giovi321/ios-backup-machine/app/webui.py

#!/usr/bin/env python3
"""
webui.py - Web UI for iOS Backup Machine settings.

Provides a web interface to configure:
- General settings (date, backup dir, owner info)
- WiFi
- NTP
- Notifications (webhook, MQTT)
- WireGuard client
- Web UI interface binding
All configuration is saved directly to config.yaml.
"""
import os, sys, time, subprocess, json, secrets, yaml, copy, hashlib, glob, plistlib, logging, shlex, shutil, threading
from functools import wraps
from logging.handlers import RotatingFileHandler

from flask import (
    Flask, render_template, request, redirect, url_for,
    flash, jsonify, send_from_directory, session
)

import netutil
import wg_crypto
import wg_manager
import wifi_manager
import host_key
import sync_crypto
import sync_manager
import notify_crypto
import config_schema
import power
import logutil

VERSION = "4.11.1"

CONFIG_PATH = os.getenv("IOSBACKUP_CONFIG", "/root/iosbackupmachine/config.yaml")
STATIC_DIR = os.path.join(os.path.dirname(os.path.abspath(__file__)), "webui_static")
TEMPLATE_DIR = os.path.join(os.path.dirname(os.path.abspath(__file__)), "webui_templates")

app = Flask(
    __name__,
    template_folder=TEMPLATE_DIR,
    static_folder=STATIC_DIR,
    static_url_path="/static"
)

# The only upload is /api/import-config, and an exported config.yaml is a few KB
# (the shipped example is 5 KB). Without a cap, picking the wrong file in the
# browser — a photo, a backup archive — has api_import_config read the whole body
# into RAM and hand it to PyYAML on a 512 MB board. 256 KB is ~50x a real config
# and stays under Flask's own 500 KB form-field limit, so this is always the
# limit that bites first and the number in the 413 message is always the true one.
MAX_UPLOAD_BYTES = 256 * 1024
app.config["MAX_CONTENT_LENGTH"] = MAX_UPLOAD_BYTES

# A wholesale wrong file can mistype every key in DEFAULTS; show the first few
# and leave the rest to webui.log rather than burying the page in banners.
IMPORT_WARNING_LIMIT = 10

@app.context_processor
def inject_version():
    return {"app_version": VERSION,
            "config_warnings": config_schema.get_load_warnings(),
            "pending_confirm": _pending_confirm()}

# Persistent logs on the rootfs; runtime status/flags on the volatile zram
# /var/log. See logutil.py for the rationale.
LOG_DIR = logutil.LOG_DIR
RUNTIME_DIR = logutil.RUNTIME_DIR

# --- Logging setup ---
os.makedirs(LOG_DIR, exist_ok=True)
os.makedirs(RUNTIME_DIR, exist_ok=True)
_log_handler = RotatingFileHandler(
    os.path.join(LOG_DIR, "webui.log"), maxBytes=2*1024*1024, backupCount=3
)
_log_handler.setFormatter(logging.Formatter("%(asctime)s [%(levelname)s] %(message)s", datefmt="%Y-%m-%d %H:%M:%S"))
_log_handler.setLevel(logging.INFO)
app.logger.addHandler(_log_handler)
app.logger.setLevel(logging.INFO)
logging.getLogger("werkzeug").setLevel(logging.WARNING)

# ---------------------------------------------------------------------------
# Config helpers
# ---------------------------------------------------------------------------

def load_config():
    # config_schema is the single source of defaults + the migration step.
    return config_schema.load_config(CONFIG_PATH)

def _apply_defaults(cfg):
    # Kept for backward compatibility; defaults now live in config_schema.
    return config_schema.apply_defaults(cfg)

# ---------------------------------------------------------------------------
# Authentication helpers
# ---------------------------------------------------------------------------

def _hash_password(password):
    """Hash a password using SHA-256 + salt (no bcrypt dependency needed)."""
    salt = secrets.token_hex(16)
    h = hashlib.sha256((salt + password).encode("utf-8")).hexdigest()
    return f"{salt}${h}"

def _verify_password(password, stored_hash):
    """Verify password against stored salt$hash."""
    if not stored_hash or "$" not in stored_hash:
        return False
    salt, h = stored_hash.split("$", 1)
    return hashlib.sha256((salt + password).encode("utf-8")).hexdigest() == h

def _auth_enabled():
    cfg = load_config()
    return bool(cfg.get("auth", {}).get("password_hash", ""))

def login_required(f):
    @wraps(f)
    def decorated(*args, **kwargs):
        if _setup_needed():
            return redirect(url_for("setup"))
        if _auth_enabled() and not session.get("authenticated"):
            return redirect(url_for("login", next=request.path))
        return f(*args, **kwargs)
    return decorated

def save_config(cfg):
    # Atomic write (tmp + fsync + rename) — a power loss mid-save can no longer
    # truncate config.yaml.
    config_schema.atomic_save(cfg, CONFIG_PATH)


def _try_save_config(cfg):
    """Persist config from a request handler; on failure flash the reason and
    return False so the caller can re-render/redirect instead of 500ing."""
    try:
        save_config(cfg)
        return True
    except Exception as e:
        app.logger.exception("Could not save configuration")
        flash(f"Could not save configuration: {e}", "error")
        return False


# ---------------------------------------------------------------------------
# WiFi multi-network helpers
# ---------------------------------------------------------------------------
def _wifi_networks(cfg):
    """Return the configured WiFi networks as a list of {nickname, ssid, password}.
    Falls back to the single legacy ssid/password if no networks list exists yet."""
    wifi = cfg.get("wifi", {}) or {}
    nets = wifi.get("networks")
    if nets:
        return nets
    ssid = (wifi.get("ssid") or "").strip()
    if ssid:
        return [{"nickname": "", "ssid": ssid, "password": wifi.get("password", "")}]
    return []


def _wifi_nickname_for(cfg, ssid):
    """Nickname configured for ``ssid`` (the live connected network), or ''."""
    if not ssid:
        return ""
    for net in _wifi_networks(cfg):
        if (net.get("ssid") or "") == ssid:
            return (net.get("nickname") or "").strip()
    return ""

# ---------------------------------------------------------------------------
# First-start / secret-key helpers
# ---------------------------------------------------------------------------

_PLACEHOLDER_KEYS = {"", "change-me", "change-me-to-a-random-string"}

def _ensure_secret_key():
    """
    If the secret_key in config.yaml is a placeholder (or empty),
    generate a cryptographically random one and persist it.
    Returns the (possibly new) secret key.
    """
    cfg = load_config()
    webui = cfg.get("webui", {})
    current = webui.get("secret_key", "")
    if current in _PLACEHOLDER_KEYS:
        new_key = secrets.token_hex(32)
        webui["secret_key"] = new_key
        cfg["webui"] = webui
        try:
            save_config(cfg)
            app.logger.info("Auto-generated new secret key.")
        except Exception as e:
            # Keep serving with the in-memory key; sessions just won't survive
            # a restart until the config becomes writable again.
            app.logger.error("Could not persist new secret key: %s", e)
        return new_key
    return current

def _setup_needed():
    """Return True if the guided first-start wizard should be shown."""
    cfg = load_config()
    # A missing/corrupt config means the saved setup state (and password hash)
    # is gone; the wizard is the recovery path, so re-engage it rather than
    # leaving an open UI that pretends setup was done.
    if config_schema.was_load_degraded():
        return True
    return not cfg.get("setup_completed", False)

# ---------------------------------------------------------------------------
# Global error handler
# ---------------------------------------------------------------------------

@app.errorhandler(Exception)
def _unhandled_error(e):
    """Log the full traceback and render a friendly page instead of the Werkzeug
    500. Debug stays off, so nothing internal leaks to the browser."""
    from werkzeug.exceptions import HTTPException
    if isinstance(e, HTTPException):
        return e
    app.logger.exception("Unhandled error on %s %s", request.method, request.path)
    try:
        return render_template("error.html"), 500
    except Exception:
        return "Something went wrong — see the Logs page.", 500

@app.errorhandler(413)
def _upload_too_large(e):
    """_unhandled_error hands HTTPExceptions straight back, so an oversized POST
    lands on Werkzeug's bare "Request Entity Too Large" page with no sidebar and
    no way back. Refuse it the way every other refused action is refused: a flash
    and a redirect to the page the user was on."""
    app.logger.warning("Rejected oversized %s to %s (%s bytes)",
                       request.method, request.path, request.content_length)
    flash(f"Upload rejected: the request was larger than the "
          f"{MAX_UPLOAD_BYTES // 1024} KB limit. An exported config.yaml is only "
          "a few KB, so check you picked the right file.", "error")
    return redirect(request.referrer or url_for("settings_general"))

# ---------------------------------------------------------------------------
# Routes
# ---------------------------------------------------------------------------

@app.route("/setup", methods=["GET", "POST"])
def setup():
    """Guided first-start wizard."""
    cfg = load_config()
    if not _setup_needed():
        return redirect(url_for("index"))

    # Detect connected iPhone for encryption & device filter steps
    connected_udid = wg_crypto.get_iphone_udid()
    connected_name = ""
    if connected_udid:
        try:
            r = subprocess.run(["ideviceinfo", "-k", "DeviceName"],
                               capture_output=True, text=True, timeout=5)
            connected_name = r.stdout.strip() if r.returncode == 0 else ""
        except Exception:
            pass

    current_time = time.strftime("%Y-%m-%dT%H:%M")

    if request.method == "POST":
        # Pairing is handled via /api/pair AJAX call before form submit.
        # Re-detect iPhone in case it was paired during this session.
        connected_udid = wg_crypto.get_iphone_udid()

        # --- Step 1: Owner info ---
        owner = []
        for i in range(4):
            owner.append(request.form.get(f"owner_line_{i}", ""))
        cfg["owner_lines"] = owner

        # --- Step 2: WiFi ---
        # The setup wizard collects a single network; it seeds wifi.networks so
        # the rest of the app (and the WiFi settings page) use the same model.
        wifi = cfg.get("wifi", {})
        wifi["enabled"] = request.form.get("wifi_enabled") == "on"
        wifi_ssid = request.form.get("wifi_ssid", "").strip()
        wifi_password = request.form.get("wifi_password", "")
        wifi["ssid"] = wifi_ssid
        wifi["password"] = wifi_password
        wifi["networks"] = ([{"nickname": "", "ssid": wifi_ssid, "password": wifi_password}]
                            if wifi_ssid else [])
        cfg["wifi"] = wifi
        if wifi["enabled"] and wifi_ssid:
            _apply_wifi_networks(wifi["networks"])

        # --- Step 3: Date/Time & NTP ---
        new_dt = request.form.get("setup_datetime", "").strip()
        if new_dt and new_dt != current_time:
            try:
                subprocess.run(["date", "-s", new_dt.replace("T", " ")],
                               capture_output=True, text=True, timeout=5)
                # Update RTC
                try:
                    import socket
                    s = socket.create_connection(("127.0.0.1", 8423), timeout=5)
                    s.sendall(b"rtc_pi2rtc\n")
                    time.sleep(0.5)
                    s.close()
                except Exception:
                    pass
                flash("Date/time updated.", "success")
            except Exception as e:
                flash(f"Failed to set date: {e}", "warning")

        ntp = cfg.get("ntp", {})
        ntp["enabled"] = request.form.get("ntp_enabled") == "on"
        servers = request.form.get("ntp_servers", "").strip().splitlines()
        ntp["servers"] = [s.strip() for s in servers if s.strip()]
        cfg["ntp"] = ntp

        # --- Step 4: Backup directory ---
        bd = request.form.get("backup_dir", "").strip()
        if bd:
            cfg["backup_dir"] = bd

        # --- Step 5: Backup encryption ---
        enc_pw = request.form.get("encryption_password", "").strip()
        enc_pw_confirm = request.form.get("encryption_password_confirm", "").strip()
        if enc_pw:
            if enc_pw != enc_pw_confirm:
                flash("Encryption passwords do not match.", "error")
                return render_template("setup.html", cfg=cfg,
                                       connected_udid=connected_udid,
                                       connected_name=connected_name,
                                       current_time=current_time)
            if connected_udid:
                try:
                    r = subprocess.run(
                        ["idevicebackup2", "encryption", "on", enc_pw,
                         cfg.get("backup_dir", "/media/iosbackup/")],
                        capture_output=True, text=True, timeout=60
                    )
                    out = r.stdout + r.stderr
                    if r.returncode == 0 or "enabled" in out.lower():
                        enc = cfg.get("backup_encryption", {})
                        enc["encryption_confirmed"] = True
                        cfg["backup_encryption"] = enc
                        flash("Backup encryption enabled on your iPhone.", "success")
                    else:
                        flash(f"Could not enable encryption: {out[:150]}. "
                              "Go to Encryption settings later to retry.", "warning")
                except subprocess.TimeoutExpired:
                    flash("Encryption command timed out. Make sure iPhone is unlocked. "
                          "You can retry from the Encryption page.", "warning")
                except Exception as e:
                    flash(f"Encryption error: {e}. You can retry from the Encryption page.", "warning")
            else:
                flash("No iPhone connected - encryption password was NOT stored. "
                      "Connect your iPhone and visit the Encryption page to enable it.", "warning")

        # --- Step 6: Device filter ---
        df = cfg.get("device_filter", {})
        df["enabled"] = request.form.get("filter_enabled") == "on"
        if connected_udid and request.form.get("add_connected_device") == "on":
            allowed = df.get("allowed_devices", [])
            existing_udids = [d.get("udid", "") for d in allowed]
            if connected_udid not in existing_udids:
                name = connected_name or "iPhone"
                allowed.append({"udid": connected_udid, "name": name})
                df["allowed_devices"] = allowed
                flash(f"Added device: {name} ({connected_udid})", "success")
        cfg["device_filter"] = df

        # --- Step 7: Notifications ---
        notif = cfg.get("notifications", {})
        # Webhook
        wh = notif.get("webhook", {})
        wh["enabled"] = request.form.get("webhook_enabled") == "on"
        wh["url"] = request.form.get("webhook_url", "")
        wh_events = request.form.getlist("webhook_events")
        if wh_events:
            wh["events"] = wh_events
        notif["webhook"] = wh
        # MQTT
        mq = notif.get("mqtt", {})
        mq["enabled"] = request.form.get("mqtt_enabled") == "on"
        mq["broker"] = request.form.get("mqtt_broker", "")
        try:
            mq["port"] = int(request.form.get("mqtt_port", "1883"))
        except ValueError:
            mq["port"] = 1883
        mq["username"] = request.form.get("mqtt_username", "")
        mq["password"] = request.form.get("mqtt_password", "")
        mq["topic_prefix"] = request.form.get("mqtt_topic_prefix", "iosbackupmachine")
        mq_events = request.form.getlist("mqtt_events")
        if mq_events:
            mq["events"] = mq_events
        notif["mqtt"] = mq
        cfg["notifications"] = notif

        # --- Step 8: Orientation ---
        orient = request.form.get("orientation", "")
        if orient:
            cfg["orientation"] = orient

        # --- Step 9: Web UI password ---
        pw = request.form.get("password", "").strip()
        if pw:
            confirm = request.form.get("confirm_password", "")
            if pw != confirm:
                flash("Passwords do not match.", "error")
                return render_template("setup.html", cfg=cfg,
                                       connected_udid=connected_udid,
                                       connected_name=connected_name,
                                       current_time=current_time)
            if len(pw) < 4:
                flash("Password must be at least 4 characters.", "error")
                return render_template("setup.html", cfg=cfg,
                                       connected_udid=connected_udid,
                                       connected_name=connected_name,
                                       current_time=current_time)
            auth = cfg.get("auth", {})
            auth["password_hash"] = _hash_password(pw)
            cfg["auth"] = auth
            session["authenticated"] = True

        cfg["setup_completed"] = True
        if not _try_save_config(cfg):
            return redirect(url_for("setup"))

        # If iPhone is connected, restart the backup service so it picks up
        # the newly-completed setup without requiring a re-plug.
        if connected_udid:
            try:
                subprocess.run(["systemctl", "restart", "iosbackupmachine.service"],
                               capture_output=True, timeout=5)
            except Exception:
                pass

        flash("Setup complete! Your iOS Backup Machine is ready.", "success")
        return redirect(url_for("index"))

    return render_template("setup.html", cfg=cfg,
                           connected_udid=connected_udid,
                           connected_name=connected_name,
                           current_time=current_time)

@app.route("/login", methods=["GET", "POST"])
def login():
    if _setup_needed():
        return redirect(url_for("setup"))
    if not _auth_enabled():
        return redirect(url_for("index"))
    if request.method == "POST":
        pw = request.form.get("password", "")
        cfg = load_config()
        stored = cfg.get("auth", {}).get("password_hash", "")
        if _verify_password(pw, stored):
            session["authenticated"] = True
            next_url = request.args.get("next", url_for("index"))
            return redirect(next_url)
        flash("Incorrect password.", "error")
    return render_template("login.html")

@app.route("/logout")
def logout():
    session.pop("authenticated", None)
    flash("Logged out.", "success")
    return redirect(url_for("login"))

def _read_backup_status():
    """Read backup status from the status file written by iosbackupmachine.py."""
    status_file = os.path.join(RUNTIME_DIR, "backup_status.json")
    try:
        if os.path.exists(status_file):
            with open(status_file, "r") as f:
                return json.load(f)
    except Exception:
        pass
    return None


def _get_storage_info():
    """Get storage info for backup drive and root."""
    info = {}
    for name, path in [("root", "/"), ("backup", load_config().get("backup_dir", "/media/iosbackup/"))]:
        try:
            st = os.statvfs(path)
            total = st.f_blocks * st.f_frsize
            free = st.f_bavail * st.f_frsize
            used = total - free
            info[name] = {
                "total": _human_size(total),
                "used": _human_size(used),
                "free": _human_size(free),
                "percent": round(used / total * 100, 1) if total > 0 else 0,
            }
        except Exception:
            info[name] = None
    return info

@app.route("/")
@login_required
def index():
    cfg = load_config()
    ip, iface_type = netutil.get_active_ip()
    wg_status = wg_manager.get_wireguard_status(cfg.get("wireguard", {}).get("interface_name", "wg0"))
    backup_status = _read_backup_status()
    storage = _get_storage_info()
    wifi_ssid = netutil.get_wifi_ssid()
    connectivity.ensure_started()
    return render_template("index.html", cfg=cfg, ip=ip, iface_type=iface_type,
                           wg_status=wg_status, backup_status=backup_status, storage=storage,
                           wifi_ssid=wifi_ssid, wifi_nickname=_wifi_nickname_for(cfg, wifi_ssid),
                           connectivity=connectivity.snapshot())

@app.route("/favicon.ico")
def favicon():
    return send_from_directory(STATIC_DIR, "favicon.ico", mimetype="image/x-icon")

# --- General Settings ---
@app.route("/settings/general", methods=["GET", "POST"])
@login_required
def settings_general():
    cfg = load_config()
    if request.method == "POST":
        cfg["backup_dir"] = request.form.get("backup_dir", cfg["backup_dir"])
        cfg["marker_file"] = request.form.get("marker_file", cfg["marker_file"])
        cfg["disk_device"] = request.form.get("disk_device", cfg["disk_device"])
        cfg["orientation"] = request.form.get("orientation", cfg["orientation"])
        cfg["font_path"] = request.form.get("font_path", cfg["font_path"])
        # Owner lines
        owner = []
        for i in range(4):
            owner.append(request.form.get(f"owner_line_{i}", ""))
        cfg["owner_lines"] = owner
        if _try_save_config(cfg):
            flash("General settings saved.", "success")
        return redirect(url_for("settings_general"))
    return render_template("settings_general.html", cfg=cfg)

# --- Date/Time ---
@app.route("/settings/datetime", methods=["GET", "POST"])
@login_required
def settings_datetime():
    cfg = load_config()
    current_time = time.strftime("%Y-%m-%dT%H:%M")
    if request.method == "POST":
        action = request.form.get("action", "")
        if action == "set_date":
            new_dt = request.form.get("datetime", "")
            if new_dt:
                try:
                    subprocess.run(["date", "-s", new_dt.replace("T", " ")],
                                   capture_output=True, text=True, timeout=5)
                    # Update RTC
                    try:
                        import socket
                        s = socket.create_connection(("127.0.0.1", 8423), timeout=5)
                        s.sendall(b"rtc_pi2rtc\n")
                        time.sleep(0.5)
                        s.close()
                    except Exception:
                        pass
                    flash("Date/time updated.", "success")
                except Exception as e:
                    flash(f"Failed to set date: {e}", "error")
        elif action == "ntp_sync":
            try:
                r = subprocess.run(
                    [sys.executable, os.path.join(os.path.dirname(__file__), "ntp-sync.py")],
                    capture_output=True, text=True, timeout=30,
                    env={**os.environ, "IOSBACKUP_CONFIG": CONFIG_PATH}
                )
                if r.returncode == 0:
                    flash("NTP sync completed.", "success")
                else:
                    flash(f"NTP sync failed: {r.stderr[:200]}", "error")
            except Exception as e:
                flash(f"NTP sync error: {e}", "error")
        elif action == "save_ntp":
            ntp = cfg.get("ntp", {})
            ntp["enabled"] = request.form.get("ntp_enabled") == "on"
            servers = request.form.get("ntp_servers", "").strip().splitlines()
            ntp["servers"] = [s.strip() for s in servers if s.strip()]
            cfg["ntp"] = ntp
            if _try_save_config(cfg):
                flash("NTP settings saved.", "success")
        elif action == "set_timezone":
            tz = request.form.get("timezone", "").strip()
            if tz:
                try:
                    subprocess.run(["timedatectl", "set-timezone", tz],
                                   capture_output=True, text=True, timeout=5, check=True)
                    flash(f"Timezone set to {tz}.", "success")
                except subprocess.CalledProcessError as e:
                    flash(f"Invalid timezone: {tz}", "error")
                except Exception as e:
                    flash(f"Failed to set timezone: {e}", "error")
        elif action == "sync_browser":
            browser_time = request.form.get("browser_time", "").strip()
            if browser_time:
                try:
                    subprocess.run(["date", "-s", browser_time],
                                   capture_output=True, text=True, timeout=5)
                    try:
                        import socket as _sock
                        s = _sock.create_connection(("127.0.0.1", 8423), timeout=5)
                        s.sendall(b"rtc_pi2rtc\n")
                        time.sleep(0.5)
                        s.close()
                    except Exception:
                        pass
                    flash("Clock synced with your browser.", "success")
                except Exception as e:
                    flash(f"Failed to sync: {e}", "error")
        return redirect(url_for("settings_datetime"))
    # Get current timezone
    current_tz = ""
    try:
        r = subprocess.run(["timedatectl", "show", "--property=Timezone", "--value"],
                           capture_output=True, text=True, timeout=5)
        current_tz = r.stdout.strip()
    except Exception:
        pass
    return render_template("settings_datetime.html", cfg=cfg, current_time=current_time,
                           current_tz=current_tz)

# --- WiFi ---
@app.route("/settings/wifi", methods=["GET", "POST"])
@login_required
def settings_wifi():
    cfg = load_config()
    if request.method == "POST":
        # Parse the dynamic rows. The three fields are parallel lists; a row is
        # kept only if it has an SSID (nickname and password are optional).
        nicknames = request.form.getlist("nickname")
        ssids = request.form.getlist("ssid")
        passwords = request.form.getlist("password")
        networks = []
        for i, ssid in enumerate(ssids):
            ssid = (ssid or "").strip()
            if not ssid:
                continue
            networks.append({
                "nickname": (nicknames[i] if i < len(nicknames) else "").strip(),
                "ssid": ssid,
                "password": passwords[i] if i < len(passwords) else "",
            })
        wifi = cfg.get("wifi", {})
        wifi["enabled"] = request.form.get("wifi_enabled") == "on"
        wifi["networks"] = networks
        # Keep the legacy single-network fields mirrored to the first entry so
        # older readers (and a downgrade) still see a sane value.
        wifi["ssid"] = networks[0]["ssid"] if networks else ""
        wifi["password"] = networks[0]["password"] if networks else ""
        cfg["wifi"] = wifi
        if not _try_save_config(cfg):
            return redirect(url_for("settings_wifi"))
        if wifi["enabled"] and networks:
            ok, msg = _apply_wifi_networks(networks)
            flash(f"WiFi settings saved. {msg}" if ok
                  else f"Saved, but applying WiFi failed: {msg}",
                  "success" if ok else "error")
        else:
            flash("WiFi settings saved.", "success")
        return redirect(url_for("settings_wifi"))
    wifi_ip = netutil.get_wifi_ip()
    wifi_ssid = netutil.get_wifi_ssid()
    return render_template("settings_wifi.html", cfg=cfg, wifi_ip=wifi_ip,
                           wifi_ssid=wifi_ssid,
                           wifi_nickname=_wifi_nickname_for(cfg, wifi_ssid),
                           wifi_networks=_wifi_networks(cfg))

@app.route("/settings/wifi/connect", methods=["POST"])
@login_required
def wifi_connect_inrange():
    """Force a scan and connect to any saved network that's in range."""
    cfg = load_config()
    if not cfg.get("wifi", {}).get("enabled"):
        flash("Enable WiFi and save first.", "error")
        return redirect(url_for("settings_wifi"))
    networks = _wifi_networks(cfg)
    if not networks:
        flash("No WiFi networks configured yet.", "error")
        return redirect(url_for("settings_wifi"))
    ok, info = wifi_manager.scan_and_connect(networks)
    if ok:
        nick = _wifi_nickname_for(cfg, info)   # info is the connected SSID
        label = f"{nick} ({info})" if nick else info
        flash(f"Connected to {label}.", "success")
    else:
        app.logger.error("WiFi scan/connect failed: %s", info)
        flash(info, "error")
    return redirect(url_for("settings_wifi"))

def _apply_wifi_networks(networks):
    """Apply the configured WiFi networks via netplan (see wifi_manager). The
    device has no NetworkManager, so WiFi is managed by writing a netplan drop-in
    and letting wpa_supplicant associate to whichever configured network is in
    range. Returns (ok, message); callers surface the message to the user."""
    ok, msg = wifi_manager.apply_networks(networks)
    if not ok:
        app.logger.error("WiFi apply failed: %s", msg)
    return ok, msg

# --- Notifications ---
@app.route("/settings/notifications", methods=["GET", "POST"])
@login_required
def settings_notifications():
    cfg = load_config()
    if request.method == "POST":
        notif = cfg.get("notifications", {})
        # Webhook
        wh = notif.get("webhook", {})
        wh["enabled"] = request.form.get("webhook_enabled") == "on"
        wh["url"] = request.form.get("webhook_url", "")
        wh_events = request.form.getlist("webhook_events")
        wh["events"] = wh_events
        # Optional auth header. The header NAME is stored in config; the VALUE is
        # encrypted into notify.enc (same credential store as WireGuard/sync).
        wh["auth_enabled"] = request.form.get("webhook_auth_enabled") == "on"
        wh["auth_header"] = (request.form.get("webhook_auth_header", "").strip()
                             or "Authorization")
        auth_value = request.form.get("webhook_auth_value", "")
        if auth_value.strip():
            mode = cfg.get("credential_encryption", {}).get("passphrase_mode", "udid")
            pw = (wg_crypto.get_iphone_serial() if mode == "udid"
                  else request.form.get("master_password", "").strip())
            if not pw:
                flash("Connect iPhone first." if mode == "udid"
                      else "Master password required to save the webhook auth header.", "error")
            elif notify_crypto.encrypt_notify_config(
                    {"header": wh["auth_header"], "value": auth_value.strip()}, passphrase=pw):
                flash("Webhook auth header encrypted and saved.", "success")
            else:
                flash("Failed to encrypt the webhook auth header.", "error")
        notif["webhook"] = wh
        # MQTT
        mq = notif.get("mqtt", {})
        mq["enabled"] = request.form.get("mqtt_enabled") == "on"
        mq["broker"] = request.form.get("mqtt_broker", "")
        try:
            mq["port"] = int(request.form.get("mqtt_port", "1883"))
        except ValueError:
            mq["port"] = 1883
        mq["username"] = request.form.get("mqtt_username", "")
        mq["password"] = request.form.get("mqtt_password", "")
        mq["topic_prefix"] = request.form.get("mqtt_topic_prefix", "iosbackupmachine")
        mq_events = request.form.getlist("mqtt_events")
        mq["events"] = mq_events
        notif["mqtt"] = mq
        cfg["notifications"] = notif
        if not _try_save_config(cfg):
            return redirect(url_for("settings_notifications"))
        # Drop the cached auth header: the URL, the header name or the secret
        # itself may have just changed, and a stale cached value would keep
        # being sent (and rejected) until the next reboot.
        try:
            import notifications as _notif
            _notif.clear_auth_cache()
        except Exception:
            pass
        flash("Notification settings saved.", "success")
        return redirect(url_for("settings_notifications"))
    return render_template("settings_notifications.html", cfg=cfg,
                           has_notify_enc=os.path.exists(notify_crypto.ENC_FILE))

@app.route("/settings/notifications/test", methods=["POST"])
@login_required
def test_notification():
    """Send a test notification via a specific channel or both."""
    from notifications import send_notification, _send_webhook, _send_mqtt, webhook_auth_headers
    channel = request.form.get("channel", "all")
    cfg = load_config()
    ncfg = cfg.get("notifications", {})
    payload = {
        "event": "test",
        "timestamp": __import__("time").strftime("%Y-%m-%dT%H:%M:%S%z"),
        "source": "iosbackupmachine",
        "message": "Test notification from iOS Backup Machine",
    }
    if channel == "webhook":
        wh = ncfg.get("webhook", {})
        if wh.get("url"):
            extra = webhook_auth_headers(wh)
            if extra is None:
                # Auth is configured but could not be obtained. Sending anyway
                # guarantees a rejection and would report it as a network fault;
                # name the real cause instead. (send_notification makes the same
                # check — this path calls _send_webhook directly and must repeat it.)
                flash("Webhook test not sent: the auth header could not be decrypted. "
                      "Connect the iPhone, or run one backup with it connected so the "
                      "header is cached.", "error")
            else:
                status, err = _send_webhook(wh["url"], payload, extra)
                if status and 200 <= status < 300:
                    flash(f"Webhook test sent successfully (HTTP {status}).", "success")
                else:
                    detail = err or (f"status {status}" if status else "no response")
                    flash(f"Webhook test failed ({detail}).", "error")
        else:
            flash("No webhook URL configured.", "error")
    elif channel == "mqtt":
        mq = ncfg.get("mqtt", {})
        if mq.get("broker"):
            topic = f"{mq.get('topic_prefix', 'iosbackupmachine')}/test"
            ok = _send_mqtt(mq["broker"], mq.get("port", 1883),
                            mq.get("username", ""), mq.get("password", ""),
                            topic, payload)
            if ok:
                flash("MQTT test sent successfully.", "success")
            else:
                flash("MQTT test failed. Check broker settings.", "error")
        else:
            flash("No MQTT broker configured.", "error")
    else:
        send_notification("test", {"message": "Test notification from iOS Backup Machine"})
        flash("Test notification sent to all enabled channels.", "success")
    return redirect(url_for("settings_notifications"))

# --- WireGuard ---
@app.route("/settings/wireguard", methods=["GET", "POST"])
@login_required
def settings_wireguard():
    cfg = load_config()
    wg = cfg.get("wireguard", {})
    iface = wg.get("interface_name", "wg0")
    wg_status = wg_manager.get_wireguard_status(iface)
    udid = wg_crypto.get_iphone_udid()
    has_enc_file = os.path.exists(wg_crypto.ENC_FILE)

    if request.method == "POST":
        action = request.form.get("action", "")
        if action == "save_settings":
            wg["enabled"] = request.form.get("wg_enabled") == "on"
            wg["auto_connect"] = request.form.get("auto_connect") == "on"
            wg["auto_connect_on"] = request.form.getlist("auto_connect_on")
            wg["interface_name"] = request.form.get("interface_name", "wg0")
            wg["full_tunnel"] = request.form.get("full_tunnel") == "on"
            cfg["wireguard"] = wg
            cred_enc = cfg.get("credential_encryption", {})
            cred_enc["passphrase_mode"] = request.form.get("passphrase_mode", "udid")
            cfg["credential_encryption"] = cred_enc
            if not _try_save_config(cfg):
                return redirect(url_for("settings_wireguard"))
            # Apply (or clear) the full-tunnel routing right away if the VPN is
            # already up; otherwise it takes effect on the next connect.
            if wg_manager.is_interface_up(iface):
                if wg["full_tunnel"]:
                    wg_manager.enforce_full_tunnel(iface)
                else:
                    wg_manager.clear_full_tunnel(iface)
            flash("WireGuard settings saved.", "success")
        elif action == "upload_config":
            wg_conf = request.form.get("wg_config", "")
            mode = cfg.get("credential_encryption", {}).get("passphrase_mode", "udid")
            pw = wg_crypto.get_iphone_serial() if mode == "udid" else request.form.get("master_password", "").strip()
            if not wg_conf.strip():
                flash("Empty WireGuard config.", "error")
            elif not pw:
                flash("Connect iPhone first." if mode == "udid" else "Password required.", "error")
            elif wg_crypto.encrypt_wg_config({"wg_conf": wg_conf}, passphrase=pw):
                flash("WireGuard config encrypted and saved.", "success")
            else:
                flash("Failed to encrypt WireGuard config.", "error")
        elif action == "start":
            mode = cfg.get("credential_encryption", {}).get("passphrase_mode", "udid")
            pw = wg_crypto.get_iphone_serial() if mode == "udid" else request.form.get("master_password", "").strip()
            ok, err = wg_manager.start_wireguard(iface, passphrase=pw)
            if ok:
                flash(f"WireGuard interface {iface} started.", "success")
            else:
                flash(f"Failed to start WireGuard: {err}", "error")
        elif action == "stop":
            if wg_manager.stop_wireguard(iface):
                flash(f"WireGuard interface {iface} stopped.", "success")
            else:
                flash("Failed to stop WireGuard.", "error")
        return redirect(url_for("settings_wireguard"))
    mode = cfg.get("credential_encryption", {}).get("passphrase_mode", "udid")
    return render_template("settings_wireguard.html",
                           cfg=cfg, wg_status=wg_status, udid=udid,
                           has_enc_file=has_enc_file, passphrase_mode=mode)

# --- Remote Sync ---
@app.route("/settings/sync", methods=["GET", "POST"])
@login_required
def settings_sync():
    cfg = load_config()
    sync = cfg.get("sync", {})
    udid = wg_crypto.get_iphone_udid()
    has_enc_file = os.path.exists(sync_crypto.ENC_FILE)

    if request.method == "POST":
        action = request.form.get("action", "")
        if action == "save_settings":
            sync["enabled"] = request.form.get("sync_enabled") == "on"
            sync["auto_sync"] = request.form.get("auto_sync") == "on"
            sync["allowed_network"] = request.form.get("allowed_network", "any")
            sync["allowed_ssid"] = request.form.get("allowed_ssid", "").strip()
            # Entered in minutes, stored in seconds. Blank or 0 means no cap, which
            # is the default: the stall watchdogs already kill a sync that has
            # stopped moving, and a first sync of a large backup set legitimately
            # runs for hours. Anything unparseable is treated as no cap rather than
            # silently reinstating one.
            try:
                _cap_min = int(float(request.form.get("max_minutes", "0") or 0))
            except (TypeError, ValueError):
                _cap_min = 0
            sync["max_seconds"] = max(0, _cap_min) * 60
            cfg["sync"] = sync
            if _try_save_config(cfg):
                flash("Sync settings saved.", "success")
        elif action == "upload_credentials":
            mode = cfg.get("credential_encryption", {}).get("passphrase_mode", "udid")
            pw = wg_crypto.get_iphone_serial() if mode == "udid" else request.form.get("master_password", "").strip()
            host = request.form.get("host", "").strip()
            port = request.form.get("port", "22").strip()
            username = request.form.get("username", "").strip()
            auth_method = request.form.get("auth_method", "key")
            ssh_key = request.form.get("ssh_key", "").replace("\r\n", "\n").replace("\r", "\n")
            password = request.form.get("password", "")
            remote_path = request.form.get("remote_path", "").strip()
            verify_host_key = request.form.get("verify_host_key") == "on"
            fingerprint_input = request.form.get("host_key_fingerprint", "").strip()
            if not pw:
                flash("Connect iPhone first." if mode == "udid" else "Password required.", "error")
            elif not host or not username or not remote_path:
                flash("Host, username, and remote path are required.", "error")
            else:
                try:
                    port_int = int(port)
                except ValueError:
                    port_int = 22
                existing_key = ""
                existing_pw = ""
                existing_fp = ""
                if not ssh_key.strip() or not password or not fingerprint_input:
                    try:
                        prev = sync_crypto.decrypt_sync_config(passphrase=pw)
                        if prev:
                            existing_key = prev.get("ssh_key", "")
                            existing_pw = prev.get("password", "")
                            existing_fp = prev.get("host_key_fingerprint", "")
                    except Exception:
                        pass
                final_key = ssh_key if ssh_key.strip() else existing_key
                final_pw = password if password else existing_pw
                # Unticking the checkbox is the only way to turn verification
                # off, so a blank field can safely mean "keep what's stored".
                final_fp = ""
                if verify_host_key:
                    try:
                        final_fp = host_key.normalize_fingerprint(fingerprint_input or existing_fp)
                    except ValueError as e:
                        flash(str(e), "error")
                        return redirect(url_for("settings_sync"))
                    if not final_fp:
                        flash("Enter the server's SHA256 host key fingerprint, or untick host key verification.", "error")
                        return redirect(url_for("settings_sync"))
                if auth_method == "key" and not final_key.strip():
                    flash("SSH private key is required for key authentication.", "error")
                    return redirect(url_for("settings_sync"))
                elif auth_method == "password" and not final_pw:
                    flash("Password is required for password authentication.", "error")
                    return redirect(url_for("settings_sync"))
                cred = {
                    "host": host, "port": port_int, "username": username,
                    "auth_method": auth_method,
                    "ssh_key": final_key if auth_method == "key" else "",
                    "password": final_pw if auth_method == "password" else "",
                    "remote_path": remote_path,
                    "host_key_fingerprint": final_fp,
                }
                if sync_crypto.encrypt_sync_config(cred, passphrase=pw):
                    flash("Sync credentials encrypted and saved.", "success")
                else:
                    flash("Failed to encrypt sync credentials.", "error")
        elif action == "test_connection":
            mode = cfg.get("credential_encryption", {}).get("passphrase_mode", "udid")
            pw = wg_crypto.get_iphone_serial() if mode == "udid" else request.form.get("master_password", "").strip()
            result = sync_manager.test_connection(passphrase=pw)
            flash(result["message"], "success" if result["success"] else "error")
        elif action == "run_sync":
            _cur = _read_backup_status() or {}
            if _cur.get("state") == "syncing":
                flash("Sync is already in progress.", "error")
            # Mutual exclusion, same check the dashboard button makes. backup-sync.py
            # still refuses to run during a backup, but its guard no longer writes the
            # status file (that write clobbered the backup's own state), so the
            # launcher is now the only place the user can be told.
            elif _backup_in_progress():
                flash("A backup is in progress. Wait for it to finish (or use auto-sync).", "error")
            else:
                # Nuke leftovers from a cancelled/crashed sync before relaunching
                try:
                    subprocess.run(["pkill", "-9", "-f", "backup-sync.py"],
                                   capture_output=True, timeout=5)
                    subprocess.run(["pkill", "-9", "-f", "/usr/bin/rsync"],
                                   capture_output=True, timeout=5)
                    time.sleep(0.3)
                except Exception:
                    pass
                sync_script = os.path.join(os.path.dirname(os.path.abspath(__file__)), "backup-sync.py")
                try:
                    _launch_sync_detached(sync_script)
                    flash("Sync started. Check the dashboard for progress.", "success")
                except Exception as e:
                    flash(f"Failed to start sync: {e}", "error")
        return redirect(url_for("settings_sync"))
    mode = cfg.get("credential_encryption", {}).get("passphrase_mode", "udid")
    saved_cred = None
    if has_enc_file:
        try:
            pw = wg_crypto.get_iphone_serial() if mode == "udid" else None
            if pw:
                dec = sync_crypto.decrypt_sync_config(passphrase=pw)
                if dec:
                    saved_cred = {
                        "host": dec.get("host", ""),
                        "port": dec.get("port", 22),
                        "username": dec.get("username", ""),
                        "auth_method": dec.get("auth_method", "key"),
                        "remote_path": dec.get("remote_path", ""),
                        "host_key_fingerprint": dec.get("host_key_fingerprint", ""),
                    }
        except Exception:
            pass
    return render_template("settings_sync.html",
                           cfg=cfg, udid=udid, has_enc_file=has_enc_file,
                           passphrase_mode=mode, saved_cred=saved_cred,
                           backup_status=_read_backup_status())

@app.route("/api/sync/decrypt", methods=["POST"])
@login_required
def api_sync_decrypt():
    """Return full decrypted sync credentials as JSON (excluding sensitive fields in the key)."""
    cfg = load_config()
    mode = cfg.get("credential_encryption", {}).get("passphrase_mode", "udid")
    pw = wg_crypto.get_iphone_serial() if mode == "udid" else None
    if not pw:
        return jsonify({"error": "iPhone not connected"}), 400
    try:
        dec = sync_crypto.decrypt_sync_config(passphrase=pw)
    except Exception as e:
        # A corrupt sync.enc must surface as a clean JSON error, not a 500.
        app.logger.exception("Failed to decrypt sync credentials")
        return jsonify({"error": f"Cannot decrypt credentials: {e}"}), 400
    if not dec:
        return jsonify({"error": "Cannot decrypt credentials"}), 400
    return jsonify({
        "host": dec.get("host", ""),
        "port": dec.get("port", 22),
        "username": dec.get("username", ""),
        "auth_method": dec.get("auth_method", "key"),
        "remote_path": dec.get("remote_path", ""),
        "host_key_fingerprint": dec.get("host_key_fingerprint", ""),
        "has_key": bool(dec.get("ssh_key", "").strip()),
        "has_password": bool(dec.get("password", "")),
    })

@app.route("/api/sync/host-key-scan", methods=["POST"])
@login_required
def api_sync_host_key_scan():
    """Report the SSH host keys a server currently offers, for the settings form.

    This is an *unauthenticated* view of the server — it is only a convenience
    for filling the field, so the response also carries the command to confirm
    the value out-of-band. Host and port come from the form rather than the
    stored credentials, so the fingerprint can be fetched before saving.
    """
    data = request.get_json(silent=True) or {}
    host = str(data.get("host", "")).strip()
    try:
        port = int(data.get("port") or 22)
    except (TypeError, ValueError):
        port = 22
    if not host:
        return jsonify({"error": "Enter the host first."}), 400
    try:
        entries = host_key.fetch_fingerprints(host, port)
    except host_key.HostKeyError as e:
        return jsonify({"error": str(e)}), 400
    except Exception as e:
        return jsonify({"error": f"Cannot read the host key: {e}"}), 400
    if not entries:
        return jsonify({"error": f"{host} returned no host key."}), 400
    return jsonify({
        "keys": [{"type": e["type"], "bits": e["bits"], "fingerprint": e["fingerprint"]}
                 for e in entries],
        "confirm_hint": "Confirm on the server with: "
                        "ssh-keygen -lf /etc/ssh/ssh_host_ed25519_key.pub",
    })

# --- Web UI Interface Binding ---
@app.route("/settings/webui", methods=["GET", "POST"])
@login_required
def settings_webui():
    cfg = load_config()
    if request.method == "POST":
        webui = cfg.get("webui", {})
        try:
            webui["port"] = int(request.form.get("port", "8080"))
        except ValueError:
            webui["port"] = 8080
        bind = request.form.getlist("bind_interfaces")
        webui["bind_interfaces"] = bind if bind else ["all"]
        webui["secret_key"] = request.form.get("secret_key", webui.get("secret_key", ""))
        cfg["webui"] = webui
        if _try_save_config(cfg):
            flash("Web UI settings saved. Restart the service to apply binding changes.", "success")
        return redirect(url_for("settings_webui"))
    interfaces = netutil.get_all_interfaces()
    return render_template("settings_webui.html", cfg=cfg, interfaces=interfaces)

# --- Password Management ---
@app.route("/settings/password", methods=["GET", "POST"])
@login_required
def settings_password():
    cfg = load_config()
    has_password = bool(cfg.get("auth", {}).get("password_hash", ""))
    if request.method == "POST":
        action = request.form.get("action", "")
        if action == "set_password":
            current = request.form.get("current_password", "")
            new_pw = request.form.get("new_password", "")
            confirm = request.form.get("confirm_password", "")
            stored = cfg.get("auth", {}).get("password_hash", "")
            # If password is already set, verify current
            if stored and not _verify_password(current, stored):
                flash("Current password is incorrect.", "error")
                return redirect(url_for("settings_password"))
            if not new_pw:
                flash("New password cannot be empty.", "error")
                return redirect(url_for("settings_password"))
            if new_pw != confirm:
                flash("New passwords do not match.", "error")
                return redirect(url_for("settings_password"))
            if len(new_pw) < 4:
                flash("Password must be at least 4 characters.", "error")
                return redirect(url_for("settings_password"))
            auth = cfg.get("auth", {})
            auth["password_hash"] = _hash_password(new_pw)
            cfg["auth"] = auth
            if not _try_save_config(cfg):
                return redirect(url_for("settings_password"))
            session["authenticated"] = True
            flash("Password updated successfully.", "success")
        elif action == "remove_password":
            current = request.form.get("current_password", "")
            stored = cfg.get("auth", {}).get("password_hash", "")
            if stored and not _verify_password(current, stored):
                flash("Current password is incorrect.", "error")
                return redirect(url_for("settings_password"))
            auth = cfg.get("auth", {})
            auth["password_hash"] = ""
            cfg["auth"] = auth
            if _try_save_config(cfg):
                flash("Password removed. Web UI is now open.", "success")
        return redirect(url_for("settings_password"))
    return render_template("settings_password.html", cfg=cfg, has_password=has_password)

# --- Device Filter ---
@app.route("/settings/devices", methods=["GET", "POST"])
@login_required
def settings_devices():
    cfg = load_config()
    df = cfg.get("device_filter", {})
    # Detect currently connected device
    connected_udid = wg_crypto.get_iphone_udid()
    connected_name = ""
    if connected_udid:
        try:
            r = subprocess.run(["ideviceinfo", "-k", "DeviceName"],
                               capture_output=True, text=True, timeout=5)
            connected_name = r.stdout.strip() if r.returncode == 0 else ""
        except Exception:
            pass

    if request.method == "POST":
        action = request.form.get("action", "")
        if action == "save_filter":
            df["enabled"] = request.form.get("filter_enabled") == "on"
            cfg["device_filter"] = df
            if _try_save_config(cfg):
                flash("Device filter settings saved.", "success")
        elif action == "add_connected":
            if not connected_udid:
                flash("No iPhone connected.", "error")
            else:
                allowed = df.get("allowed_devices", [])
                existing_udids = [d.get("udid", "") for d in allowed]
                if connected_udid in existing_udids:
                    flash(f"Device {connected_udid} is already in the list.", "warning")
                else:
                    name = connected_name or request.form.get("device_name", "Unknown")
                    allowed.append({"udid": connected_udid, "name": name})
                    df["allowed_devices"] = allowed
                    cfg["device_filter"] = df
                    if _try_save_config(cfg):
                        flash(f"Added device: {name} ({connected_udid})", "success")
        elif action == "add_manual":
            udid = request.form.get("manual_udid", "").strip()
            name = request.form.get("manual_name", "").strip() or "Manual entry"
            if not udid:
                flash("UDID cannot be empty.", "error")
            else:
                allowed = df.get("allowed_devices", [])
                existing_udids = [d.get("udid", "") for d in allowed]
                if udid in existing_udids:
                    flash(f"Device {udid} is already in the list.", "warning")
                else:
                    allowed.append({"udid": udid, "name": name})
                    df["allowed_devices"] = allowed
                    cfg["device_filter"] = df
                    if _try_save_config(cfg):
                        flash(f"Added device: {name} ({udid})", "success")
        elif action == "remove_device":
            rm_udid = request.form.get("remove_udid", "")
            allowed = df.get("allowed_devices", [])
            df["allowed_devices"] = [d for d in allowed if d.get("udid") != rm_udid]
            cfg["device_filter"] = df
            if _try_save_config(cfg):
                flash(f"Device {rm_udid} removed.", "success")
        return redirect(url_for("settings_devices"))
    return render_template("settings_devices.html", cfg=cfg, df=df,
                           connected_udid=connected_udid, connected_name=connected_name)

# --- Backup Settings ---
@app.route("/settings/backup", methods=["GET", "POST"])
@login_required
def settings_backup():
    cfg = load_config()
    if request.method == "POST":
        bk = cfg.get("backup", {})
        bk["auto_start"] = request.form.get("auto_start") == "on"
        bk["notify_on_rejected"] = request.form.get("notify_on_rejected") == "on"
        cfg["backup"] = bk
        if _try_save_config(cfg):
            flash("Backup settings saved.", "success")
        return redirect(url_for("settings_backup"))
    return render_template("settings_backup.html", cfg=cfg)

# --- Backup Encryption ---
@app.route("/settings/encryption", methods=["GET", "POST"])
@login_required
def settings_encryption():
    cfg = load_config()
    enc = cfg.get("backup_encryption", {})
    connected_udid = wg_crypto.get_iphone_udid()

    # Check current encryption status on device
    enc_status = None
    if connected_udid:
        # Try ideviceinfo with backup domain (where WillEncrypt lives)
        try:
            r = subprocess.run(
                ["ideviceinfo", "--domain", "com.apple.mobile.backup", "-k", "WillEncrypt"],
                capture_output=True, text=True, timeout=10
            )
            val = r.stdout.strip().lower()
            if r.returncode == 0 and val:
                if val in ("true", "1"):
                    enc_status = "enabled"
                elif val in ("false", "0"):
                    enc_status = "disabled"
        except Exception:
            pass
        # Fallback: run idevicebackup2 and parse output
        if enc_status is None:
            try:
                r = subprocess.run(
                    ["idevicebackup2", "backup", "--dry-run", cfg.get("backup_dir", "/media/iosbackup/")],
                    capture_output=True, text=True, timeout=15
                )
                out = (r.stdout + r.stderr).lower()
                if "will be encrypted" in out or "backup encryption is currently enabled" in out:
                    enc_status = "enabled"
                elif "will not be encrypted" in out or "backup encryption is currently disabled" in out:
                    enc_status = "disabled"
            except Exception:
                pass
        # Last fallback: check if encryption was ever confirmed during a backup
        if enc_status is None and cfg.get("backup_encryption", {}).get("encryption_confirmed"):
            enc_status = "enabled"

    if request.method == "POST":
        action = request.form.get("action", "")
        if action == "enable_encryption":
            pw = request.form.get("enable_password", "").strip()
            if not pw:
                flash("Please provide an encryption password.", "error")
            elif not connected_udid:
                flash("No iPhone connected. Connect your iPhone first.", "error")
            else:
                try:
                    r = subprocess.run(
                        ["idevicebackup2", "encryption", "on", pw, cfg.get("backup_dir", "/media/iosbackup/")],
                        capture_output=True, text=True, timeout=60
                    )
                    out = r.stdout + r.stderr
                    if r.returncode == 0 or "enabled" in out.lower():
                        enc["encryption_confirmed"] = True
                        cfg["backup_encryption"] = enc
                        if _try_save_config(cfg):
                            flash("Backup encryption enabled on device. The password was NOT stored - remember it for restores.", "success")
                    else:
                        flash(f"Failed to enable encryption: {out[:200]}", "error")
                except subprocess.TimeoutExpired:
                    flash("Command timed out. Make sure the iPhone is unlocked and trusted.", "error")
                except Exception as e:
                    flash(f"Error enabling encryption: {e}", "error")
        elif action == "change_password":
            old_pw = request.form.get("old_password", "").strip()
            new_pw = request.form.get("new_password", "").strip()
            if not old_pw or not new_pw:
                flash("Both old and new passwords are required.", "error")
            elif not connected_udid:
                flash("No iPhone connected. Connect your iPhone first.", "error")
            else:
                try:
                    r = subprocess.run(
                        ["idevicebackup2", "changepw", old_pw, new_pw, cfg.get("backup_dir", "/media/iosbackup/")],
                        capture_output=True, text=True, timeout=60
                    )
                    out = r.stdout + r.stderr
                    if r.returncode == 0:
                        flash("Encryption password changed on device. The new password was NOT stored - remember it for restores.", "success")
                    else:
                        flash(f"Failed to change password: {out[:200]}", "error")
                except Exception as e:
                    flash(f"Error changing password: {e}", "error")
        return redirect(url_for("settings_encryption"))
    return render_template("settings_encryption.html",
                           cfg=cfg, enc=enc, connected_udid=connected_udid, enc_status=enc_status)

# --- Backup List ---

def _dir_size(path):
    """Return total size in bytes of all files under *path*."""
    total = 0
    try:
        for dirpath, _dirnames, filenames in os.walk(path):
            for f in filenames:
                fp = os.path.join(dirpath, f)
                try:
                    total += os.path.getsize(fp)
                except OSError:
                    pass
    except OSError:
        pass
    return total

def _human_size(nbytes):
    for unit in ("B", "KB", "MB", "GB", "TB"):
        if abs(nbytes) < 1024:
            return f"{nbytes:.1f} {unit}"
        nbytes /= 1024
    return f"{nbytes:.1f} PB"

app.jinja_env.filters["human_size"] = _human_size


def _human_duration(seconds):
    """Compact duration for the dashboard. Same shape as the sync log's, so an
    ETA read on the dashboard and one read in the log look alike."""
    try:
        seconds = int(seconds)
    except (TypeError, ValueError):
        return ""
    if seconds < 60:
        return f"{seconds}s"
    if seconds < 3600:
        return f"{seconds // 60}m"
    return f"{seconds // 3600}h{(seconds % 3600) // 60:02d}m"

app.jinja_env.filters["human_duration"] = _human_duration


class ConnectivityMonitor:
    """Background internet probe, cached for the dashboard and the health endpoint.

    ``netutil.have_connectivity()`` opens a TCP connection and blocks for up to
    its timeout per host, twice when both fail — so probing inline would make the
    status poll as slow as the outage it is meant to report, and would put a
    packet on the resolvers every few seconds for every open browser tab. This
    probes on its own schedule; readers get the cached answer.

    It also records when the current state began. That is the number that matters
    on this device: the iPhone hotspot can drop as a sync starts and the device
    fails over to WiFi, and "offline for 3m" says that happened where a bare
    "offline" does not.
    """

    def __init__(self, interval=20.0):
        self.interval = interval
        self._lock = threading.Lock()
        self._online = None        # None until the first probe lands
        self._checked_at = 0.0
        self._changed_at = 0.0
        self._thread = None

    def ensure_started(self):
        """Start the probe loop once, on first use.

        Deliberately not started at import: importing this module must not open
        sockets, or the test suite would depend on the network.
        """
        with self._lock:
            if self._thread is not None:
                return
            self._thread = threading.Thread(target=self._loop, daemon=True)
        self._thread.start()

    def _loop(self):
        while True:
            self.probe_once()
            time.sleep(self.interval)

    def probe_once(self):
        """Run one probe and fold it into the cached state. Never raises."""
        try:
            online = bool(netutil.have_connectivity(timeout=4))
        except Exception:
            online = False
        now = time.time()
        with self._lock:
            if online != self._online:
                self._changed_at = now
            self._online = online
            self._checked_at = now
        return online

    def snapshot(self):
        """Current state: ``online`` is None while no probe has completed yet,
        which readers must render as "checking" rather than as offline."""
        now = time.time()
        with self._lock:
            return {
                "online": self._online,
                "age_seconds": int(now - self._checked_at) if self._checked_at else None,
                "since_seconds": int(now - self._changed_at) if self._changed_at else None,
                "interval_seconds": int(self.interval),
            }


connectivity = ConnectivityMonitor()


def _health_internet(monitor=None):
    """Internet state for the health endpoint.

    Prefers the monitor's cached answer so the endpoint stays fast, but probes
    directly when the cache is empty or stale: an external monitor polling
    /api/health must not be told the wrong thing just because nobody has opened
    the dashboard recently. ``monitor`` is injectable for tests.
    """
    monitor = connectivity if monitor is None else monitor
    monitor.ensure_started()
    snap = monitor.snapshot()
    age = snap["age_seconds"]
    if snap["online"] is not None and age is not None and age <= monitor.interval * 2:
        return snap["online"]
    return monitor.probe_once()

def _parse_info_plist(plist_path):
    """Parse an iOS backup Info.plist and return a dict of useful fields."""
    info = {}
    try:
        with open(plist_path, "rb") as fp:
            pl = plistlib.load(fp)
        info["device_name"] = pl.get("Device Name", "")
        info["display_name"] = pl.get("Display Name", "")
        info["product_type"] = pl.get("Product Type", "")
        info["product_version"] = pl.get("Product Version", "")
        info["serial_number"] = pl.get("Serial Number", "")
        info["udid"] = pl.get("Target Identifier", "") or pl.get("Unique Identifier", "")
        last_backup = pl.get("Last Backup Date")
        if last_backup:
            info["last_backup"] = last_backup.strftime("%Y-%m-%d %H:%M:%S")
            info["last_backup_ts"] = last_backup.timestamp()
        else:
            info["last_backup"] = ""
            info["last_backup_ts"] = 0
    except Exception:
        pass
    return info

@app.route("/backups")
@login_required
def backups():
    cfg = load_config()
    backup_dir = cfg.get("backup_dir", "/media/iosbackup/")
    backup_list = []
    if os.path.isdir(backup_dir):
        for entry in os.listdir(backup_dir):
            entry_path = os.path.join(backup_dir, entry)
            if not os.path.isdir(entry_path):
                continue
            info_plist = os.path.join(entry_path, "Info.plist")
            if not os.path.exists(info_plist):
                continue
            info = _parse_info_plist(info_plist)
            # Folder modification time as fallback date
            try:
                stat = os.stat(entry_path)
                folder_mtime = time.strftime("%Y-%m-%d %H:%M:%S", time.localtime(stat.st_mtime))
                folder_mtime_ts = stat.st_mtime
            except OSError:
                folder_mtime = ""
                folder_mtime_ts = 0
            # Size calculated asynchronously via /api/backup-sizes
            # Check for Manifest.plist (indicates a completed backup)
            has_manifest = os.path.exists(os.path.join(entry_path, "Manifest.plist"))
            # Check for Status.plist snapshot state
            status_plist = os.path.join(entry_path, "Status.plist")
            snapshot_state = ""
            if os.path.exists(status_plist):
                try:
                    with open(status_plist, "rb") as fp:
                        st = plistlib.load(fp)
                    snapshot_state = st.get("SnapshotState", "")
                except Exception:
                    pass
            # Determine human-readable status
            if has_manifest and snapshot_state != "uploading":
                status = "complete"
                status_label = "Complete"
            elif snapshot_state == "uploading":
                status = "backing_up"
                status_label = "Backing up"
            elif has_manifest:
                status = "complete"
                status_label = "Complete"
            else:
                status = "interrupted"
                status_label = "Interrupted"

            backup_list.append({
                "folder": entry,
                "device_name": info.get("display_name") or info.get("device_name") or entry,
                "product_type": info.get("product_type", ""),
                "ios_version": info.get("product_version", ""),
                "serial": info.get("serial_number", ""),
                "udid": info.get("udid", entry),
                "size": "...",
                "last_backup": info.get("last_backup") or folder_mtime,
                "sort_ts": info.get("last_backup_ts") or folder_mtime_ts,
                "status": status,
                "status_label": status_label,
            })
    # Sort newest first
    backup_list.sort(key=lambda b: b["sort_ts"], reverse=True)
    sync_enabled = cfg.get("sync", {}).get("enabled", False)
    return render_template("backups.html", cfg=cfg, backups=backup_list,
                           backup_dir=backup_dir, sync_enabled=sync_enabled)

# --- Log Viewer ---
# The Logs page is what the user opens once something has already gone wrong,
# so it must not be the next thing to break: view_log used to f.read() the whole
# file and hand it to Jinja to escape and to buffer, which costs several times
# the file in RAM on a board that has 512 MB of it, and a single runaway run can
# leave a very large log. A run log is read from both ends anyway - a backup's
# gates ([CMD], mount, free space, encryption) are at the top and what it died
# of is at the bottom - so the viewer shows both and the download link covers
# the middle.
LOG_VIEW_HEAD_LINES = int(os.getenv("IOSBACKUP_LOG_VIEW_HEAD_LINES", "40"))
LOG_VIEW_TAIL_LINES = int(os.getenv("IOSBACKUP_LOG_VIEW_TAIL_LINES", "500"))
# Hard ceiling on the read whatever the lines look like: a writer wedged
# mid-line leaves a file with no newline in it at all, and a line-counting tail
# on that one reads the whole thing - the exact failure being bounded here.
LOG_VIEW_MAX_BYTES = int(os.getenv("IOSBACKUP_LOG_VIEW_MAX_BYTES",
                                   str(256 * 1024)))

def _decode_lines(raw):
    # Read as bytes and decode with "replace": a window that opens or closes
    # inside a multi-byte character then renders one U+FFFD instead of raising.
    return raw.decode("utf-8", "replace").splitlines(True)

def _read_bounded(path, head_lines, tail_lines, max_bytes):
    """Read the head and the tail of a log without holding the file in memory.

    Returns (text, truncated, size). When truncated, the two halves are
    separated by one notice line naming what is not shown.
    """
    head_bytes = max(1, max_bytes // 8)           # the failure is at the end,
    tail_bytes = max(1, max_bytes - head_bytes)   # so the tail gets the bulk
    with open(path, "rb") as f:
        # fstat on the handle rather than a separate getsize: the size then
        # always describes the inode the bytes came from.
        size = os.fstat(f.fileno()).st_size
        if size <= max_bytes:
            head, tail, windowed = _decode_lines(f.read()), [], False
        else:
            head = _decode_lines(f.read(head_bytes))
            f.seek(size - tail_bytes)
            tail, windowed = _decode_lines(f.read(tail_bytes)), True
    if windowed:
        # Drop the half lines the two windows end and start in, but only while a
        # whole line survives: a log with no newline in it would otherwise come
        # back empty, which is worse than a fragment.
        if len(head) > 1 and not head[-1].endswith("\n"):
            head.pop()
        if len(tail) > 1:
            tail.pop(0)
    elif len(head) <= head_lines + tail_lines:
        return "".join(head), False, size         # short enough to show whole
    else:
        # Under the byte ceiling but past what anyone reads on a phone: split
        # the lines already in hand rather than returning the head alone.
        whole = head
        head, tail = whole[:head_lines], whole[-tail_lines:]
    head = head[:head_lines]
    tail = tail[-tail_lines:]
    text = "".join(head)
    if text and not text.endswith("\n"):
        text += "\n"
    text += ("\n[web UI] showing the first %d and the last %d lines of this "
             "%s log; download it for what is in between\n\n"
             % (len(head), len(tail), _human_size(size)))
    return text + "".join(tail), True, size

@app.route("/logs")
@login_required
def logs():
    log_files = []
    current_backup_log = None
    current_sync_log = None
    if os.path.isdir(LOG_DIR):
        for f in sorted(glob.glob(os.path.join(LOG_DIR, "*.log")), reverse=True):
            stat = os.stat(f)
            # Skip empty log files
            if stat.st_size == 0:
                continue
            name = os.path.basename(f)
            log_files.append({
                "name": name,
                "size": stat.st_size,
                "mtime": time.strftime("%Y-%m-%d %H:%M:%S", time.localtime(stat.st_mtime)),
            })
            # Find the most recent backup / sync logs (for "View Live" links)
            if name.startswith("backup-") and current_backup_log is None:
                current_backup_log = name
            if name.startswith("sync-") and current_sync_log is None:
                current_sync_log = name
    return render_template("logs.html", log_files=log_files,
                           current_backup_log=current_backup_log,
                           current_sync_log=current_sync_log)

@app.route("/logs/<filename>")
@login_required
def view_log(filename):
    # Sanitize filename
    safe = os.path.basename(filename)
    path = os.path.join(LOG_DIR, safe)
    content = ""
    truncated = False
    size = 0
    if os.path.isfile(path):
        try:
            content, truncated, size = _read_bounded(
                path, LOG_VIEW_HEAD_LINES, LOG_VIEW_TAIL_LINES,
                LOG_VIEW_MAX_BYTES)
        except Exception as e:
            content = f"Error reading log: {e}"
    else:
        content = "Log file not found."
    if request.args.get("raw"):
        # What the live tail re-fetches: the same bounded text the page already
        # shows, as plain text, so following a log costs one bounded read
        # instead of a full template render and a DOM parse every two seconds.
        return app.response_class(content, mimetype="text/plain")
    return render_template("log_view.html", filename=safe, content=content,
                           truncated=truncated, size=size)

@app.route("/logs/<filename>/download")
@login_required
def download_log(filename):
    """The whole file, for what the bounded view leaves out. send_from_directory
    streams it in 8 KB chunks through the WSGI file wrapper, so the escape hatch
    cannot reintroduce the buffering the bounded read exists to avoid."""
    safe = os.path.basename(filename)
    if not os.path.isfile(os.path.join(LOG_DIR, safe)):
        flash(f"Log file not found: {safe}", "error")
        return redirect(url_for("logs"))
    return send_from_directory(LOG_DIR, safe, as_attachment=True,
                               mimetype="text/plain")

@app.route("/logs/<filename>/delete", methods=["POST"])
@login_required
def delete_log(filename):
    safe = os.path.basename(filename)
    path = os.path.join(LOG_DIR, safe)
    if os.path.isfile(path):
        try:
            os.remove(path)
            flash(f"Deleted {safe}.", "success")
        except Exception as e:
            flash(f"Failed to delete {safe}: {e}", "error")
    else:
        flash(f"Log file not found: {safe}", "error")
    return redirect(url_for("logs"))

@app.route("/logs/purge", methods=["POST"])
@login_required
def purge_logs():
    count = 0
    if os.path.isdir(LOG_DIR):
        for f in glob.glob(os.path.join(LOG_DIR, "*.log")):
            # The running process holds webui.log open; deleting it would
            # silently kill web UI logging until the next restart.
            if os.path.basename(f) == "webui.log":
                continue
            try:
                os.remove(f)
                count += 1
            except Exception:
                pass
    flash(f"Purged {count} log file(s).", "success")
    return redirect(url_for("logs"))

# --- System journal ---
# Both long-running units log with StandardOutput=journal, and the hardening
# pass put much of its diagnostics only there: "[WARN] display init failed",
# "[DRAW] display still unavailable", "[WATCHDOG] ...", "[FATAL] main loop
# stalled". Without this page that whole class of daemon-level degradation is
# reachable only over SSH, on a device whose premise is that the web UI is the
# only interface anyone needs. webui.service runs as root, so journalctl sees
# every unit.
JOURNAL_ALL = "*"          # not a legal unit name, so it cannot collide with one
JOURNAL_UNITS = [
    ("iosbackupmachine",   "Display daemon (iosbackupmachine)"),
    ("webui",              "Web UI (webui)"),
    ("backup-sync",        "Sync, started by the button (backup-sync)"),
    ("iosbackup-web-sync", "Sync, started from the web UI (iosbackup-web-sync)"),
    ("iosbackup-update",   "Update (iosbackup-update)"),
    ("usbmuxd",            "iPhone USB daemon (usbmuxd)"),
    ("pisugar-server",     "Battery (pisugar-server)"),
    (JOURNAL_ALL,          "Everything (all units and the kernel)"),
]
JOURNAL_LINE_CHOICES = [200, 500, 1000, 2000]
JOURNAL_DEFAULT_LINES = 500
# journalctl walks backwards from the tail; for a unit that logs rarely that
# walk can cross the whole journal. Flask's server is threaded, so an overrun
# costs one worker thread rather than the UI, but it still has to end by itself.
JOURNAL_TIMEOUT = 10
# Reading the journal header is cheap, so it gets the same 5s the other probes
# in this file use.
JOURNAL_BOOTS_TIMEOUT = 5
# One journal line has no length bound (a traceback, an rsync path). Cap what is
# handed to Jinja so opening this page during a flood is not what finally takes
# the web UI out.
JOURNAL_MAX_CHARS = 256 * 1024
# The daemons' own vocabulary, not journalctl's. These lines are plain print()
# to stdout, which systemd records at SyslogLevel= (info) unless the text starts
# with a "<N>" prefix - none do - so "journalctl -p warning" would look correct
# and return nothing. Match on what is actually written instead.
_JOURNAL_TRUNC_PREFIX = "[... truncated"

# The first group is the daemons' vocabulary. The second is this app's own: Flask
# leaves its default_handler on app.logger, so every app.logger.warning/.error
# also reaches webui.service's journal formatted "[ts] WARNING in webui: ...",
# which none of the bracket tags above match - the filter answered "nothing
# matched" on a journal full of web UI errors.
JOURNAL_MARKERS = ("[FATAL]", "[ERROR]", "[WATCHDOG]", "[WARN]", "[DRAW]",
                   "[WG]", "Traceback",
                   "] WARNING in ", "] ERROR in ", "] CRITICAL in ")


def _read_journal(unit, lines):
    """Tail one unit's journal. Returns (text, ok).

    Never raises. This is the page a user opens when something is already
    broken, so a missing, wedged or unhappy journalctl has to render as a
    sentence that explains itself, not as the generic 500 page.
    """
    if shutil.which("journalctl") is None:
        return ("journalctl is not available on this system, so the journal "
                "cannot be shown. The log files on the Logs page are unaffected.",
                False)
    argv = ["journalctl", "-n", str(lines), "--no-pager", "--output=short-iso"]
    if unit != JOURNAL_ALL:
        argv += ["-u", unit]
    try:
        r = subprocess.run(argv, capture_output=True, text=True,
                           errors="replace", timeout=JOURNAL_TIMEOUT)
    except subprocess.TimeoutExpired:
        return (f"journalctl did not answer within {JOURNAL_TIMEOUT}s; journald "
                f"may be wedged. Try a smaller line count, or read it over SSH "
                f"with: {' '.join(argv)}", False)
    except Exception as e:
        return (f"Could not run journalctl: {e}", False)
    if r.returncode != 0:
        return ((r.stderr or r.stdout or "").strip()
                or f"journalctl exited {r.returncode}", False)
    out = r.stdout
    if len(out) > JOURNAL_MAX_CHARS:
        # Keep the tail: the newest lines are the ones explaining the failure.
        out = (f"[... truncated to the last {JOURNAL_MAX_CHARS // 1024} KB ...]\n"
               + out[-JOURNAL_MAX_CHARS:])
    return (out.strip() or "No journal entries for this unit.", True)


_journal_boots_cache = None


def _journal_boots():
    """How many boots the journal still holds, or None if it cannot be asked.

    Nothing in this repo configures journald storage and /var/log is the zram
    RAM disk (see logutil's docstring), so on a stock image the journal is
    probably current-boot-only. That is worth measuring rather than asserting: a
    page that silently shows nothing from before the last restart is worse than
    one that says so.
    """
    # Guarded here too, not only in _read_journal: opening this page must not
    # fork anything at all on a system that has no journalctl.
    # Cached for the life of the process: journald retention does not change
    # between page refreshes, and a live tail re-rendering this page every 10 s
    # forked a second journalctl each time for an answer it already had.
    global _journal_boots_cache
    if _journal_boots_cache is not None:
        return _journal_boots_cache
    if shutil.which("journalctl") is None:
        return None
    try:
        r = subprocess.run(["journalctl", "--list-boots", "--no-pager"],
                           capture_output=True, text=True, errors="replace",
                           timeout=JOURNAL_BOOTS_TIMEOUT)
    except Exception:
        return None
    if r.returncode != 0:
        return None
    n = 0
    for line in r.stdout.splitlines():
        # systemd >= 254 prints a table header ("IDX BOOT ID ..."); older
        # versions print the boot offset alone. Both start a data row with that
        # integer offset, so count those and let any header fall out. Parsing
        # beats passing --no-legend, which an older journalctl would reject as
        # an unknown option and exit non-zero on.
        head = line.split()[:1]
        if head:
            try:
                int(head[0])
                n += 1
            except ValueError:
                pass
    _journal_boots_cache = n or None
    return _journal_boots_cache


@app.route("/logs/journal")
@login_required
def journal_log():
    # The unit is looked up in the table, never passed through: a hand-edited
    # ?unit= starting with "-" would land in journalctl's argv as an option, and
    # an unknown option is a non-zero exit with nothing useful on the page.
    units = [u for u, _ in JOURNAL_UNITS]
    unit = request.args.get("unit") or units[0]
    if unit not in units:
        unit = units[0]
    try:
        lines = int(request.args.get("lines", JOURNAL_DEFAULT_LINES))
    except (TypeError, ValueError):
        lines = JOURNAL_DEFAULT_LINES
    if lines not in JOURNAL_LINE_CHOICES:
        # Snap rather than clamp: the selector and the output must agree, and a
        # bookmarked ?lines=100000 must not be a way to ask for the whole journal.
        lines = JOURNAL_DEFAULT_LINES
    content, ok = _read_journal(unit, lines)
    problems = request.args.get("problems") == "1"
    if ok and problems:
        # Filter what was already read; never a second journalctl.
        # The truncation notice is not a log line and matches no marker, but
        # dropping it hides that the window was cut, so the filtered view would
        # look like the whole story.
        kept = [ln for ln in content.splitlines()
                if any(m in ln for m in JOURNAL_MARKERS)
                or ln.startswith(_JOURNAL_TRUNC_PREFIX)]
        content = "\n".join(kept) or (
            "Nothing in this window matched " + " ".join(JOURNAL_MARKERS) + ".\n\n"
            "That is not the same as \"no problems\". These markers are the two "
            "daemons\' own vocabulary; a unit that reports trouble some other way "
            "(werkzeug, usbmuxd, the kernel) will not match. Turn the filter off "
            "to read the window in full.")
    return render_template("journal_view.html", journal_units=JOURNAL_UNITS,
                           unit=unit, lines=lines,
                           line_choices=JOURNAL_LINE_CHOICES,
                           problems=problems, boots=_journal_boots(),
                           content=content, ok=ok)

# --- System Update ---
REPO_DIR = os.getenv("IOSBACKUP_REPO", "/root/ios-backup-machine")
VERSION_FILE = os.path.join(os.path.dirname(os.path.abspath(__file__)), ".installed_version")
# Watched by the display daemon: while it exists the e-ink shows "Updating /
# Device will reboot", including on the daemon's way down. It lives on the
# volatile runtime dir, so the reboot at the end of the update clears it.
UPDATING_FILE = os.path.join(RUNTIME_DIR, "updating")

# Env the updater runs with. NONINTERACTIVE skips the two `read -rp` prompts in
# update.sh / install.sh (they get EOF from a non-tty and would otherwise answer
# "no" to both the re-install and the reboot). AUTO_REBOOT makes install.sh
# reboot when it finishes: the installer stops every service up front and only
# restarts some of them, so a web-triggered update that does not reboot can
# leave the display daemon and the WireGuard reconciler down — which is exactly
# how the device used to drop off the VPN mid-update.
UPDATE_ENV = {
    "DEBIAN_FRONTEND": "noninteractive",
    "IOSBACKUP_SKIP_VERSION_CHECK": "1",
    "IOSBACKUP_NONINTERACTIVE": "1",
    "IOSBACKUP_AUTO_REBOOT": "1",
}


def _mark_updating(marker=None):
    """Drop the sentinel the display daemon watches. Best-effort: a missing
    e-ink notice must not stop the update."""
    path = marker or UPDATING_FILE
    try:
        os.makedirs(os.path.dirname(path), exist_ok=True)
        with open(path, "w") as f:
            f.write(str(int(time.time())))
        return True
    except Exception:
        return False


def _clear_updating(marker=None):
    try:
        os.remove(marker or UPDATING_FILE)
    except Exception:
        pass


def _update_launch_command(script, log_file, have_systemd_run=None):
    """argv that runs the updater detached from webui.service.

    install.sh restarts webui.service partway through. webui.service does not set
    KillMode=process, so systemd tears down its entire cgroup on that restart —
    and a Popen(start_new_session=True) child is still inside that cgroup, only
    in a different session. So the updater used to be SIGTERMed mid-run, after
    it had stopped every service but before it restarted them or rebooted.

    systemd-run puts the updater in its own transient unit, outside the webui
    cgroup, so the restart cannot touch it. --collect reaps the unit afterwards,
    which also clears a failed unit of the same name from a previous attempt.
    Redirection is done by the inner shell rather than StandardOutput=append: so
    this does not depend on the systemd version.

    The output goes through logutil's stamper on the way to the log. update.sh is
    a shell script writing plain stdout, so it is the one log that cannot stamp
    its own lines — and an update that breaks a sync is exactly the correlation
    an unstamped log makes impossible. pipefail keeps the unit's exit status the
    updater's rather than the stamper's.
    """
    if have_systemd_run is None:
        have_systemd_run = shutil.which("systemd-run") is not None
    if not have_systemd_run:
        # No systemd-run: run it in-cgroup as before. The update still applies,
        # but it can be cut short at the webui restart.
        return ["bash", script]
    stamper = f"{shlex.quote(sys.executable)} {shlex.quote(logutil.__file__)} --stamp"
    inner = (f"set -o pipefail; bash {shlex.quote(script)} 2>&1 | "
             f"{stamper} > {shlex.quote(log_file)}")
    argv = ["systemd-run", "--unit=iosbackup-update", "--collect"]
    argv += [f"--setenv={k}={v}" for k, v in sorted(UPDATE_ENV.items())]
    argv += ["bash", "-c", inner]
    return argv


def _launch_sync_detached(sync_script):
    """Launch backup-sync.py detached from webui.service.

    A plain Popen child sits in webui.service's cgroup, so a webui restart
    (e.g. after a settings change or an update) SIGTERMs the rsync mid-run —
    the same failure mode the updater had. systemd-run puts the sync in its own
    transient unit; without systemd we fall back to cutting the session tie so
    at least a SIGHUP can't reach it.
    """
    env = {**os.environ, "IOSBACKUP_CONFIG": CONFIG_PATH}
    if shutil.which("systemd-run"):
        argv = ["systemd-run", "--unit=iosbackup-web-sync", "--collect",
                f"--setenv=IOSBACKUP_CONFIG={CONFIG_PATH}",
                sys.executable, sync_script]
        r = subprocess.run(argv, capture_output=True, text=True, timeout=30, env=env)
        if r.returncode == 0:
            return
        app.logger.warning("systemd-run sync launch failed (%s); falling back to Popen",
                           (r.stderr or r.stdout or "").strip())
    subprocess.Popen([sys.executable, sync_script],
                     stdout=subprocess.DEVNULL, stderr=subprocess.DEVNULL,
                     env=env, start_new_session=True)

@app.route("/update", methods=["GET", "POST"])
@login_required
def system_update():
    installed_version = VERSION
    try:
        if os.path.exists(VERSION_FILE):
            with open(VERSION_FILE, "r") as f:
                installed_version = f.read().strip() or VERSION
    except Exception:
        pass

    remote_version = None
    recent_commits = []
    update_log = None

    if request.method == "POST":
        action = request.form.get("action", "")

        if action == "check":
            # Fetch latest from remote
            try:
                subprocess.run(["git", "-C", REPO_DIR, "fetch", "--quiet", "origin"],
                               capture_output=True, timeout=30)
                # Get remote version from webui.py on origin/main
                r = subprocess.run(
                    ["git", "-C", REPO_DIR, "show", "origin/main:app/webui.py"],
                    capture_output=True, text=True, timeout=10
                )
                import re as _re
                m = _re.search(r'VERSION\s*=\s*"([^"]+)"', r.stdout)
                if m:
                    remote_version = m.group(1)

                # Get recent commits
                r2 = subprocess.run(
                    ["git", "-C", REPO_DIR, "log", "--oneline", "-10", "HEAD..origin/main"],
                    capture_output=True, text=True, timeout=10
                )
                recent_commits = [ln for ln in r2.stdout.strip().splitlines() if ln.strip()]
                if not recent_commits:
                    remote_version = remote_version or installed_version

                if remote_version and remote_version != installed_version:
                    flash(f"Update available: v{installed_version} -> v{remote_version}", "success")
                elif remote_version:
                    flash("Already up to date.", "success")
            except Exception as e:
                flash(f"Failed to check for updates: {e}", "error")

        elif action == "update":
            # Run update.sh detached — the installer restarts the web UI and
            # then reboots the device, so we can't wait for it to finish.
            update_script = os.path.join(REPO_DIR, "update.sh")
            # update.sh stops every service, and iosbackupmachine.service's
            # KillMode=mixed reaps idevicebackup2 with it — the same destruction
            # as a reboot, so the same refusal. Ahead of _mark_updating() so a
            # refused update never strands "Updating" on the e-ink.
            busy = _busy_with()
            if busy and not _confirmed():
                app.logger.info("Refused update: %s in progress", busy)
                flash(_BUSY_REFUSAL[busy], "error")
                # A redirect rather than the fall-through render so base.html
                # picks the offer up from ?confirm=. Content-identical: the
                # update branch never sets remote_version or recent_commits.
                return redirect(url_for("system_update", confirm="update"))
            if not os.path.isfile(update_script):
                flash("update.sh not found in repo directory.", "error")
            else:
                log_file = os.path.join(LOG_DIR, "update.log")
                try:
                    os.makedirs(LOG_DIR, exist_ok=True)
                    if busy:
                        _quiesce_for_destructive(busy)
                    # Paint the e-ink notice before anything is stopped, so the
                    # panel is already showing "Updating" when the daemon dies.
                    _mark_updating()
                    argv = _update_launch_command(update_script, log_file)
                    if argv[0] == "systemd-run":
                        # systemd-run returns as soon as the unit is started, so
                        # this can be waited on. Without the wait a refused start
                        # (e.g. iosbackup-update already active) would be silent
                        # and the e-ink would sit on "Updating" until a reboot.
                        r = subprocess.run(argv, capture_output=True, text=True,
                                           timeout=30,
                                           env={**os.environ, **UPDATE_ENV})
                        if r.returncode != 0:
                            raise RuntimeError(
                                (r.stderr or r.stdout or "").strip()
                                or f"systemd-run exited {r.returncode}")
                    else:
                        with open(log_file, "w") as lf:
                            subprocess.Popen(argv, stdout=lf, stderr=lf,
                                             env={**os.environ, **UPDATE_ENV},
                                             start_new_session=True)
                    flash("Update started. The device will reboot when it finishes — "
                          "the web UI is back about a minute later.", "success")
                except Exception as e:
                    _clear_updating()
                    flash(f"Failed to start update: {e}", "error")

        return render_template("system_update.html",
                               installed_version=installed_version,
                               remote_version=remote_version,
                               recent_commits=recent_commits,
                               update_log=update_log)

    return render_template("system_update.html",
                           installed_version=installed_version,
                           remote_version=remote_version,
                           recent_commits=recent_commits,
                           update_log=update_log)

# --- API endpoints ---
@app.route("/api/status")
@login_required
def api_status():
    cfg = load_config()
    ip, iface_type = netutil.get_active_ip()
    wg = cfg.get("wireguard", {})
    wifi_ssid = netutil.get_wifi_ssid()
    connectivity.ensure_started()
    return jsonify({
        "ip": ip,
        "interface": iface_type,
        "wifi_ip": netutil.get_wifi_ip(),
        "wifi_ssid": wifi_ssid,
        "wifi_nickname": _wifi_nickname_for(cfg, wifi_ssid),
        "usb_iphone_ip": netutil.get_usb_iphone_ip(),
        "wireguard": wg_manager.get_wireguard_status(wg.get("interface_name", "wg0")),
        "connectivity": connectivity.snapshot(),
        "time": time.strftime("%Y-%m-%d %H:%M:%S"),
    })

# --- Health endpoint ---
_HEALTH_UNITS = ["iosbackupmachine", "webui", "pisugar-server", "usbmuxd"]


def _service_states(units=None):
    """Return {unit: active|inactive|failed|unknown} via systemctl is-active."""
    states = {}
    for u in (units or _HEALTH_UNITS):
        try:
            r = subprocess.run(["systemctl", "is-active", u],
                               capture_output=True, text=True, timeout=5)
            states[u] = r.stdout.strip() or "unknown"
        except Exception:
            states[u] = "unknown"
    return states


def _iso_from_mtime(ts):
    return time.strftime("%Y-%m-%dT%H:%M:%S", time.localtime(ts))


def _last_backup_info():
    """Current backup state + newest backup folder time (best-effort), plus the
    daemon's durable record of the last SUCCESSFUL backup and whether it has gone
    stale. Folder mtimes report the last write — an interrupted run bumps them
    too — so they cannot answer "is this device still backing up".
    """
    st = _read_backup_status() or {}
    info = {
        "state": st.get("state"),
        "timestamp": st.get("timestamp"),
        "completed_at": st.get("completed_at"),
        "last_backup_time": None,
        "last_success": None,
        "last_success_ts": None,
        "stale": False,
        "age_seconds": None,
    }
    try:
        bd = load_config().get("backup_dir", "/media/iosbackup/")
        latest = None
        if os.path.isdir(bd):
            for e in os.scandir(bd):
                if e.is_dir() and os.path.exists(os.path.join(e.path, "Info.plist")):
                    m = e.stat().st_mtime
                    if latest is None or m > latest:
                        latest = m
        if latest:
            info["last_backup_time"] = _iso_from_mtime(latest)
    except Exception:
        pass
    # Its own try: a missing or corrupt record must degrade to nulls, never turn
    # /api/health (the surface an external poller watches) into a 500.
    try:
        with open(os.path.join(LOG_DIR, "last_backup.json"), "r") as f:
            rec = json.load(f)
        ts = rec.get("completed_at") if isinstance(rec, dict) else None
        if isinstance(ts, (int, float)) and not isinstance(ts, bool) and ts > 0:
            age = time.time() - ts
            info["last_success_ts"] = ts
            info["last_success"] = _iso_from_mtime(ts)
            info["age_seconds"] = int(max(0.0, age))
            thr = load_config().get("backup", {}).get("stale_after_sec", 604800)
            thr = int(thr) if isinstance(thr, int) and not isinstance(thr, bool) else 604800
            info["stale"] = bool(thr > 0 and age >= thr)
    except Exception:
        pass
    return info


def _last_sync_info():
    """Last sync result from the status file, else newest sync log mtime."""
    st = _read_backup_status() or {}
    state = st.get("state")
    if state in ("syncing", "sync_complete", "sync_error"):
        return {"state": state, "message": st.get("message"), "timestamp": st.get("timestamp")}
    try:
        logs = glob.glob(os.path.join(LOG_DIR, "sync-*.log"))
        if logs:
            newest = max(logs, key=os.path.getmtime)
            return {"state": None, "timestamp": _iso_from_mtime(os.path.getmtime(newest)),
                    "log": os.path.basename(newest)}
    except Exception:
        pass
    return {"state": None, "timestamp": None}


@app.route("/api/health")
def api_health():
    """Aggregate health for external monitoring. Login-exempt and free of
    secrets (no owner info, credentials, or keys)."""
    cfg = load_config()
    services = _service_states()
    storage = _get_storage_info()
    battery = power.get_battery()
    ip, iface_type = netutil.get_active_ip()
    wg = cfg.get("wireguard", {})
    wifi_ssid = netutil.get_wifi_ssid()
    network = {
        "active_ip": ip,
        "interface": iface_type,
        "wifi_ip": netutil.get_wifi_ip(),
        "wifi_ssid": wifi_ssid,
        "wifi_nickname": _wifi_nickname_for(cfg, wifi_ssid),
        "usb_iphone_ip": netutil.get_usb_iphone_ip(),
        "internet": _health_internet(),
        "wireguard": wg_manager.get_wireguard_status(wg.get("interface_name", "wg0")),
    }
    backup = _last_backup_info()
    sync = _last_sync_info()

    # Overall rollup
    status, warnings = "ok", []
    if services.get("iosbackupmachine") == "failed" or services.get("webui") == "failed":
        status = "error"; warnings.append("service failed")
    bd_info = storage.get("backup")
    if isinstance(bd_info, dict) and bd_info.get("percent", 0) >= 95:
        status = "error"; warnings.append("backup disk almost full")
    pct = battery.get("percent")
    thr = cfg.get("sync", {}).get("min_battery_percent", 35)
    if pct is not None and not battery.get("charging") and pct < thr and status != "error":
        status = "warning"; warnings.append("battery low")
    if not network["internet"] and status == "ok":
        status = "warning"; warnings.append("no internet")
    if backup.get("state") == "error" and status != "error":
        status = "warning"; warnings.append("last backup error")
    # The pull half of the quiet-device alert: a poller catches both "up but
    # quiet" here and "unreachable" from the poll failing, which together cover
    # the case a push notification from the device itself never can.
    if backup.get("stale") and status != "error":
        days = int((backup.get("age_seconds") or 0) // 86400)
        status = "warning"; warnings.append(f"no backup in {days} days")

    return jsonify({
        "status": status,
        "warnings": warnings,
        "version": VERSION,
        "time": time.strftime("%Y-%m-%dT%H:%M:%S"),
        "services": services,
        "disk": storage,
        "battery": battery,
        "network": network,
        "backup": backup,
        "sync": sync,
    })


@app.route("/api/pair", methods=["POST"])
def api_pair():
    """Trigger iPhone pairing (shows 'Trust this computer?' on iPhone).
    Accessible without login so the setup wizard can use it."""
    try:
        # Run idevicepair pair — this triggers the Trust prompt on the iPhone
        r = subprocess.run(["idevicepair", "pair"],
                           capture_output=True, text=True, timeout=30)
        out = (r.stdout + r.stderr).strip()

        # Check if pairing succeeded or if user needs to tap Trust
        if r.returncode == 0 and "SUCCESS" in out.upper():
            # Pairing done, get UDID
            udid = wg_crypto.get_iphone_udid()
            name = ""
            if udid:
                try:
                    nr = subprocess.run(["ideviceinfo", "-k", "DeviceName"],
                                        capture_output=True, text=True, timeout=5)
                    name = nr.stdout.strip() if nr.returncode == 0 else ""
                except Exception:
                    pass
            return jsonify({"status": "paired", "udid": udid or "", "name": name})
        elif "user denied" in out.lower() or "USER_DENIED_PAIRING" in out:
            return jsonify({"status": "denied", "message": "User denied pairing on iPhone."})
        else:
            # Pairing request sent — user needs to tap Trust on iPhone
            return jsonify({"status": "waiting", "message": "Tap 'Trust' on your iPhone, then click 'Check Connection' again."})
    except subprocess.TimeoutExpired:
        return jsonify({"status": "timeout", "message": "Pairing timed out. Make sure iPhone is unlocked."})
    except FileNotFoundError:
        return jsonify({"status": "error", "message": "idevicepair not found. Is libimobiledevice installed?"})
    except Exception as e:
        return jsonify({"status": "error", "message": str(e)})

@app.route("/api/backup-status")
@login_required
def api_backup_status():
    """API endpoint for live backup status polling."""
    status = _read_backup_status()
    return jsonify(status or {"state": "idle"})

def _cancel_sync_cleanly():
    """Kill any running rsync + backup-sync.py so a stuck/stalled sync stops
    immediately. Shared with the destructive actions, which cancel a sync this
    way before they take the device down."""
    # SIGKILL both — SIGTERM on the python process can leave it in the proc
    # table long enough that the very next "Sync Now" gets blocked by its
    # own another_sync_running() guard.
    subprocess.run(["pkill", "-9", "-f", "/usr/bin/rsync"],
                   capture_output=True, timeout=5)
    subprocess.run(["pkill", "-9", "-f", "backup-sync.py"],
                   capture_output=True, timeout=5)
    time.sleep(0.5)  # give the kernel a moment to reap
    # Mark the sync as cancelled so the dashboard / e-ink reflect it.
    try:
        os.makedirs(RUNTIME_DIR, exist_ok=True)
        from datetime import datetime as _dt
        data = {"state": "sync_error",
                "message": "Cancelled by user.",
                "timestamp": _dt.now().isoformat()}
        tmp = os.path.join(RUNTIME_DIR, "backup_status.json.tmp")
        with open(tmp, "w") as f:
            json.dump(data, f)
        os.replace(tmp, os.path.join(RUNTIME_DIR, "backup_status.json"))
    except Exception:
        pass


@app.route("/sync/cancel", methods=["POST"])
@login_required
def sync_cancel():
    """Kill any running rsync + backup-sync.py so a stuck/stalled sync stops immediately."""
    cur = _read_backup_status() or {}
    if cur.get("state") != "syncing":
        flash("No sync is running.", "error")
        return redirect(request.referrer or url_for("index"))
    try:
        _cancel_sync_cleanly()
        flash("Sync cancelled.", "success")
    except Exception as e:
        flash(f"Failed to cancel sync: {e}", "error")
    return redirect(request.referrer or url_for("index"))

@app.route("/sync/start", methods=["POST"])
@login_required
def sync_start():
    """Launch backup-sync.py as a subprocess from anywhere (e.g. dashboard button)."""
    cfg = load_config()
    if not cfg.get("sync", {}).get("enabled"):
        flash("Remote sync is disabled. Enable it in Remote Sync settings.", "error")
        return redirect(request.referrer or url_for("index"))
    cur = _read_backup_status() or {}
    if cur.get("state") == "syncing":
        flash("Sync is already in progress.", "error")
        return redirect(request.referrer or url_for("index"))
    # Mutual exclusion: don't start a sync while a backup is running.
    if _backup_in_progress():
        flash("A backup is in progress. Wait for it to finish (or use auto-sync).", "error")
        return redirect(request.referrer or url_for("index"))
    sync_script = os.path.join(os.path.dirname(os.path.abspath(__file__)), "backup-sync.py")
    if not os.path.isfile(sync_script):
        flash("backup-sync.py not found on disk.", "error")
        return redirect(request.referrer or url_for("index"))
    # State is not 'syncing' — safe to nuke any leftover backup-sync.py / rsync
    # processes from a cancelled or crashed sync, so the new launch isn't
    # blocked by its own another_sync_running() guard.
    try:
        subprocess.run(["pkill", "-9", "-f", "backup-sync.py"],
                       capture_output=True, timeout=5)
        subprocess.run(["pkill", "-9", "-f", "/usr/bin/rsync"],
                       capture_output=True, timeout=5)
        time.sleep(0.3)
    except Exception:
        pass
    try:
        _launch_sync_detached(sync_script)
        flash("Sync started. Watch the dashboard or live log for progress.", "success")
    except Exception as e:
        flash(f"Failed to start sync: {e}", "error")
    return redirect(request.referrer or url_for("index"))

@app.route("/api/backup-sizes")
@login_required
def api_backup_sizes():
    """Calculate backup folder sizes (slow — called via AJAX after page load)."""
    cfg = load_config()
    backup_dir = cfg.get("backup_dir", "/media/iosbackup/")
    sizes = {}
    if os.path.isdir(backup_dir):
        for entry in os.listdir(backup_dir):
            entry_path = os.path.join(backup_dir, entry)
            if os.path.isdir(entry_path) and os.path.exists(os.path.join(entry_path, "Info.plist")):
                sizes[entry] = _human_size(_dir_size(entry_path))
    return jsonify(sizes)

@app.route("/api/export-config")
@login_required
def api_export_config():
    """Download config.yaml as a file."""
    from flask import send_file
    if not os.path.isfile(CONFIG_PATH):
        return jsonify({"error": "No config file on disk to export."}), 404
    return send_file(CONFIG_PATH, as_attachment=True, download_name="config.yaml",
                     mimetype="text/yaml")

@app.route("/api/import-config", methods=["POST"])
@login_required
def api_import_config():
    """Upload and replace config.yaml."""
    f = request.files.get("config_file")
    if not f:
        flash("No file uploaded.", "error")
        return redirect(url_for("settings_general"))
    try:
        content = f.read().decode("utf-8")
        # Validate it's valid YAML
        cfg = yaml.safe_load(content)
        if not isinstance(cfg, dict):
            flash("Invalid config file (not a YAML dict).", "error")
            return redirect(url_for("settings_general"))
        # Migrate + default-fill the imported config, then save atomically so a
        # bad upload or power loss can't leave a half-written config.yaml.
        # Collect what the merge had to correct: apply_defaults silently swaps a
        # wrong-typed value for the default, and we save the corrected tree — so
        # the next load is clean, the degraded-config banner never fires, and the
        # user would never learn which of their settings the import dropped.
        warnings = []
        cfg = config_schema.apply_defaults(config_schema.migrate(cfg), warnings)
        save_config(cfg)
        flash("Config imported. Restart services to apply.", "success")
        if warnings:
            app.logger.warning("Config import reset %d invalid value(s): %s",
                               len(warnings), "; ".join(warnings))
            for w in warnings[:IMPORT_WARNING_LIMIT]:
                flash(f"Imported config: {w}", "warning")
            extra = len(warnings) - IMPORT_WARNING_LIMIT
            if extra > 0:
                flash(f"Imported config: {extra} more invalid value(s) were reset "
                      "to defaults; the full list is in webui.log.", "warning")
    except Exception as e:
        flash(f"Import failed: {e}", "error")
    return redirect(url_for("settings_general"))

def _iphone_connected():
    """True if at least one iPhone is currently connected (idevice_id -l)."""
    try:
        r = subprocess.run(["idevice_id", "-l"], capture_output=True, text=True, timeout=5)
        return bool(r.stdout.strip())
    except Exception:
        return False


def _backup_in_progress():
    """True if a backup is running (status or a live idevicebackup2)."""
    if (_read_backup_status() or {}).get("state") in ("backing_up", "connected"):
        return True
    try:
        # Timeout: this runs inside a request, so a wedged pgrep would hold a
        # worker open. Failing open here is deliberate — backup-sync.py's own
        # guard fails closed, so the worst case is a launch that then refuses.
        return subprocess.run(["pgrep", "-f", "idevicebackup2"],
                              capture_output=True, timeout=5).returncode == 0
    except Exception:
        return False


@app.route("/api/start-backup", methods=["POST"])
@login_required
def api_start_backup():
    """Request a backup from the always-on display daemon (used when auto-start
    is off). Drops a sentinel the daemon consumes; it backs up if an allowed
    iPhone is connected. We never restart the service — that owns the e-ink."""
    # Don't trigger a backup when no iPhone is connected.
    if not _iphone_connected():
        flash("No iPhone connected. Plug in and unlock your iPhone, then try again.", "error")
        return redirect(request.referrer or url_for("index"))
    # Mutual exclusion: don't start a backup while a sync is running.
    if (_read_backup_status() or {}).get("state") == "syncing":
        flash("A sync is in progress. Wait for it to finish, then start the backup.", "error")
        return redirect(request.referrer or url_for("index"))
    try:
        os.makedirs(RUNTIME_DIR, exist_ok=True)
        # Make sure the daemon is up (no-op if already running).
        subprocess.run(["systemctl", "start", "iosbackupmachine.service"],
                       capture_output=True, timeout=10)
        open(os.path.join(RUNTIME_DIR, "start_requested"), "w").close()
        flash("Backup requested. Make sure your iPhone is unlocked.", "success")
    except Exception as e:
        flash(f"Error: {e}", "error")
    return redirect(url_for("index"))

def _stop_backup_cleanly():
    """Signal the always-on display daemon to abort the current backup (it owns
    the e-ink and renders the interrupted screen) instead of stopping its
    service. Shared with the destructive actions, which stop a backup this way
    before they take the device down."""
    os.makedirs(RUNTIME_DIR, exist_ok=True)
    open(os.path.join(RUNTIME_DIR, "stop_requested"), "w").close()
    subprocess.run(["pkill", "-f", "idevicebackup2"],
                   capture_output=True, timeout=5)
    # Reflect the stop on the dashboard immediately (atomic write).
    try:
        status_file = os.path.join(RUNTIME_DIR, "backup_status.json")
        tmp = status_file + ".tmp"
        with open(tmp, "w") as f:
            json.dump({"state": "interrupted", "reason": "Stopped from web UI",
                       "timestamp": time.strftime("%Y-%m-%dT%H:%M:%S")}, f)
        os.replace(tmp, status_file)
    except Exception:
        pass


@app.route("/api/stop-backup", methods=["POST"])
@login_required
def api_stop_backup():
    """Abort the current backup. Signals the always-on display daemon (which owns
    the e-ink and renders the interrupted screen) instead of stopping its service."""
    try:
        _stop_backup_cleanly()
        flash("Backup stopped.", "success")
    except Exception as e:
        flash(f"Error: {e}", "error")
    return redirect(url_for("index"))

# ---------------------------------------------------------------------------
# Destructive actions
# ---------------------------------------------------------------------------
# Reboot, shutdown and update are the three actions that end in-flight work: the
# first two cut the power out from under idevicebackup2, and update.sh stops
# every service — iosbackupmachine.service's KillMode=mixed then reaps the
# idevicebackup2 child with it. A backup killed that way leaves a half-copied
# snapshot the next run has to redo, and no [INTERRUPT] line in the run log to
# say why. The harmless actions already refuse while the other one runs; these
# three did not, so one mistimed click threw the work away silently.
#
# Refuse once, then offer an explicit override — never a hard block. The owner
# must always be able to power the device off from the web UI, and
# _backup_in_progress() deliberately fails open precisely because a wedged pgrep
# must not lock them out. The override is carried by the ?confirm= argument the
# refusal redirects with, not by server-side state: it is scoped to the page the
# user lands on, disappears the moment they navigate anywhere else, and there is
# nothing to expire, leak between browsers, or clean up after a crash.
_BUSY_REFUSAL = {
    "backup": "A backup is in progress. Stop it first with Stop Backup on the "
              "dashboard, or use the button below to reboot, shut down or "
              "update anyway.",
    "sync": "A sync is in progress. Stop it first with Cancel Sync on the "
            "dashboard, or use the button below to reboot, shut down or "
            "update anyway.",
}

_CONFIRM_ACTIONS = {
    "reboot":   {"endpoint": "api_reboot",    "label": "Reboot anyway",
                 "fields": {}},
    "shutdown": {"endpoint": "api_shutdown",  "label": "Shut down anyway",
                 "fields": {}},
    "update":   {"endpoint": "system_update", "label": "Update anyway",
                 "fields": {"action": "update"}},
}


def _busy_with():
    """'backup', 'sync' or None — the in-flight work a destructive action would
    end. Sync is checked first: a leftover idevicebackup2 still matches
    _backup_in_progress()'s pgrep during a sync, and naming the wrong job sends
    the user to a button that cannot help. Fails open like the probes it wraps."""
    try:
        if (_read_backup_status() or {}).get("state") == "syncing":
            return "sync"
        if _backup_in_progress():
            return "backup"
    except Exception:
        return None
    return None


def _confirmed():
    """True if this request is the second, explicit press."""
    return request.form.get("confirm") == "1"


def _pending_confirm():
    """The "do it anyway" offer for base.html, or None. Runs on every render,
    including the 500 page, so it never raises."""
    try:
        action = request.args.get("confirm")
        spec = _CONFIRM_ACTIONS.get(action)
        return dict(spec, action=action) if spec else None
    except Exception:
        return None


# 40 x 0.25s. Bounded by iterations rather than wall clock, so a test that stubs
# time.sleep finishes instantly instead of spinning for ten seconds.
_QUIESCE_POLLS = 40
# Named so a test can tell this loop's sleeps apart from any other thread's:
# patching time.sleep patches it for the whole process, background probers
# included.
_QUIESCE_POLL_SEC = 0.25


def _note_sync_cancelled():
    """Append one line to the newest sync run log, best-effort. The persistent
    log is the only record that survives the reboot that follows."""
    try:
        logs = sorted(glob.glob(os.path.join(LOG_DIR, "sync-*.log")),
                      key=os.path.getmtime, reverse=True)
        if not logs:
            return
        with open(logs[0], "a") as f:
            f.write("[INTERRUPT] cancelled to reboot, shut down or update"
                    " the device" + chr(10))
    except Exception as e:
        app.logger.warning("Could not note the sync cancellation: %s", e)
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
