giovi321/ios-backup-machine/tests/test_logutil.py

"""Tests for logutil.prune_logs (per-run log retention) and
wg_manager.latest_handshake (WireGuard handshake-health parsing)."""
import os
import time

import logutil
import wg_manager


def _touch(path, age_seconds=0):
    open(path, "w").close()
    if age_seconds:
        t = time.time() - age_seconds
        os.utime(path, (t, t))


def test_prune_keeps_newest_n_per_kind(tmp_path):
    d = str(tmp_path)
    for i in range(60):
        _touch(os.path.join(d, f"sync-{i:04d}.log"), age_seconds=i * 60)
        _touch(os.path.join(d, f"backup-{i:04d}.log"), age_seconds=i * 60)
    logutil.prune_logs(log_dir=d, keep_per_kind=50, max_age_days=0)  # age disabled
    kept = os.listdir(d)
    assert len([f for f in kept if f.startswith("sync-")]) == 50
    assert len([f for f in kept if f.startswith("backup-")]) == 50
    # The newest survive; the oldest are gone.
    assert "sync-0000.log" in kept
    assert "sync-0059.log" not in kept


def test_prune_drops_files_past_max_age(tmp_path):
    d = str(tmp_path)
    _touch(os.path.join(d, "sync-fresh.log"), age_seconds=0)
    _touch(os.path.join(d, "sync-stale.log"), age_seconds=100 * 86400)
    logutil.prune_logs(log_dir=d, keep_per_kind=50, max_age_days=90)
    kept = os.listdir(d)
    assert "sync-fresh.log" in kept
    assert "sync-stale.log" not in kept


def test_prune_leaves_non_per_run_logs_alone(tmp_path):
    d = str(tmp_path)
    for name in ("webui.log", "ntp-sync.log", "autostart.log", "update.log"):
        _touch(os.path.join(d, name), age_seconds=1000 * 86400)  # ancient
    logutil.prune_logs(log_dir=d, keep_per_kind=1, max_age_days=1)
    kept = set(os.listdir(d))
    assert kept == {"webui.log", "ntp-sync.log", "autostart.log", "update.log"}


def test_prune_never_raises_on_missing_dir():
    logutil.prune_logs(log_dir="/nonexistent/iosbackupmachine/logs")  # must not raise


class _FakeProc:
    def __init__(self, returncode, stdout):
        self.returncode = returncode
        self.stdout = stdout


def test_latest_handshake_parses_newest(monkeypatch):
    out = "pubkeyAAA\t1700000000\npubkeyBBB\t1700000500\n"
    monkeypatch.setattr(wg_manager.subprocess, "run",
                        lambda *a, **k: _FakeProc(0, out))
    assert wg_manager.latest_handshake("wg0") == 1700000500


def test_latest_handshake_zero_when_never(monkeypatch):
    # wg prints a 0 epoch for a peer that has never handshaked.
    monkeypatch.setattr(wg_manager.subprocess, "run",
                        lambda *a, **k: _FakeProc(0, "pubkeyAAA\t0\n"))
    assert wg_manager.latest_handshake("wg0") == 0


def test_latest_handshake_none_on_error(monkeypatch):
    # A failed `wg` call means the state is unknown — None, not 0 ("no handshake").
    monkeypatch.setattr(wg_manager.subprocess, "run",
                        lambda *a, **k: _FakeProc(1, ""))
    assert wg_manager.latest_handshake("wg0") is None


# ---------------------------------------------------------------------------
# stamp_stream — the shell side of line timestamping
# ---------------------------------------------------------------------------
# update.log and the backup-sync output redirected into autostart.log are raw
# stdout from shell, so they cannot use TimestampedLog directly. They pipe
# through this instead, which reuses the same stamp so every log in the system
# reads identically.

def test_stamp_stream_prefixes_every_line():
    import io
    src = io.StringIO("first\nsecond\n")
    dst = io.StringIO()
    logutil.stamp_stream(src, dst)
    lines = dst.getvalue().splitlines()
    assert len(lines) == 2
    assert lines[0].endswith("first")
    assert lines[1].endswith("second")


def test_stamp_stream_uses_the_same_format_as_the_run_log():
    import io, re
    dst = io.StringIO()
    logutil.stamp_stream(io.StringIO("x\n"), dst)
    assert re.match(r"^\[\d{4}-\d{2}-\d{2} \d{2}:\d{2}:\d{2}\] x$", dst.getvalue().rstrip())


def test_stamp_stream_stamps_a_final_line_without_a_newline():
    import io
    dst = io.StringIO()
    logutil.stamp_stream(io.StringIO("no trailing newline"), dst)
    assert dst.getvalue().rstrip().endswith("no trailing newline")
    assert dst.getvalue().startswith("[")


def test_stamp_stream_preserves_blank_lines_without_stamping_them():
    import io
    dst = io.StringIO()
    logutil.stamp_stream(io.StringIO("a\n\nb\n"), dst)
    lines = dst.getvalue().split("\n")
    assert lines[1] == ""          # blank stays blank, no lone timestamp
    assert lines[0].endswith("a")
    assert lines[2].endswith("b")


def test_stamp_stream_strips_ansi_colour_codes():
    """install.sh colours its output; the codes are noise in a log file."""
    import io
    dst = io.StringIO()
    logutil.stamp_stream(io.StringIO("\033[0;32m  done\033[0m\n"), dst)
    out = dst.getvalue().rstrip()
    assert out.endswith("done")
    assert "\033" not in out


def test_stamp_stream_survives_undecodable_input():
    import io
    dst = io.StringIO()
    logutil.stamp_stream(io.StringIO("ok\n"), dst)
    assert "ok" in dst.getvalue()


# ---------------------------------------------------------------------------
# TimestampedLog.write — a failing disk must never reach the caller
# ---------------------------------------------------------------------------
# iosbackupmachine.py writes log lines unguarded all over, including from
# inside its own fatal handler, so an ENOSPC/EROFS from the file must be
# swallowed here. The first failure is printed to stderr (the journal) so the
# disk problem is still visible somewhere.

class _BoomFile:
    def __init__(self, fail=True):
        self.calls = 0
        self.fail = fail

    def write(self, s):
        self.calls += 1
        if self.fail:
            raise OSError(28, "No space left on device")

    def flush(self):
        pass

    def close(self):
        pass


def test_write_never_propagates_oserror(capsys):
    log = logutil.TimestampedLog(_BoomFile())
    for _ in range(3):
        log.write("line\n")                      # must not raise
    assert "[logutil] log write failed" in capsys.readouterr().err


def test_write_reports_only_the_first_failure_of_a_streak(capsys):
    log = logutil.TimestampedLog(_BoomFile())
    for _ in range(3):
        log.write("line\n")
    assert capsys.readouterr().err.count("[logutil]") == 1


def test_write_stops_hitting_the_disk_after_repeated_failures():
    fh = _BoomFile()
    log = logutil.TimestampedLog(fh)
    for _ in range(20):
        log.write("line\n")
    assert fh.calls == 10                        # then the log goes dead


def test_write_recovers_when_the_disk_does(capsys):
    fh = _BoomFile()
    log = logutil.TimestampedLog(fh)
    log.write("dropped\n")
    fh.fail = False
    log.write("back\n")
    assert fh.calls == 2                         # kept trying after one failure


def test_close_on_a_dead_log_still_does_not_raise():
    fh = _BoomFile()
    log = logutil.TimestampedLog(fh)
    log.write("partial line without newline")
    log.close()                                  # must not raise


# ---------------------------------------------------------------------------
# prune_logs — aggregate size cap per kind
# ---------------------------------------------------------------------------

def _sized(path, size, age_seconds=0):
    with open(path, "w") as f:
        f.write("x" * size)
    if age_seconds:
        t = time.time() - age_seconds
        os.utime(path, (t, t))


def test_prune_size_cap_deletes_oldest_until_under_cap(tmp_path):
    d = str(tmp_path)
    for i in range(5):                           # sync-0 oldest ... sync-4 newest
        _sized(os.path.join(d, f"sync-{i}.log"), 1000, age_seconds=(5 - i) * 60)
    logutil.prune_logs(log_dir=d, keep_per_kind=50, max_age_days=0,
                       max_bytes_per_kind=2500)
    kept = sorted(os.listdir(d))
    # 5 x 1000 B: deleting oldest first — 4000, 3000 still over — leaves 2000 B.
    assert kept == ["sync-3.log", "sync-4.log"]


def test_prune_size_cap_is_per_kind(tmp_path):
    d = str(tmp_path)
    _sized(os.path.join(d, "sync-old.log"), 1000, age_seconds=600)
    _sized(os.path.join(d, "sync-new.log"), 1000, age_seconds=60)
    _sized(os.path.join(d, "backup-old.log"), 1000, age_seconds=600)
    _sized(os.path.join(d, "backup-new.log"), 1000, age_seconds=60)
    logutil.prune_logs(log_dir=d, keep_per_kind=50, max_age_days=0,
                       max_bytes_per_kind=100)
    # Each kind is over the cap on its own and loses its oldest file; the
    # newest of each kind is the one being written and is never swept.
    assert sorted(os.listdir(d)) == ["backup-new.log", "sync-new.log"]


def test_prune_size_cap_never_deletes_the_newest_log(tmp_path):
    """The newest log is the one being written: the auto-sync prune runs while
    the daemon still holds its backup log open, where deleting it frees nothing
    until the writer closes and only makes the running job vanish from the
    Logs page."""
    d = str(tmp_path)
    _sized(os.path.join(d, "sync-new.log"), 5000, age_seconds=60)
    _sized(os.path.join(d, "sync-old.log"), 100, age_seconds=600)
    logutil.prune_logs(log_dir=d, keep_per_kind=50, max_age_days=0,
                       max_bytes_per_kind=1000)
    assert os.listdir(d) == ["sync-new.log"]


def test_prune_size_cap_leaves_logs_under_the_cap_alone(tmp_path):
    d = str(tmp_path)
    _sized(os.path.join(d, "sync-a.log"), 100)
    _sized(os.path.join(d, "sync-b.log"), 100)
    logutil.prune_logs(log_dir=d, keep_per_kind=50, max_age_days=0,
                       max_bytes_per_kind=1024)
    assert sorted(os.listdir(d)) == ["sync-a.log", "sync-b.log"]


def test_prune_default_cap_is_100mb():
    assert logutil.LOG_MAX_BYTES_PER_KIND == 100 * 1024 * 1024


# ---------------------------------------------------------------------------
# TimestampedLog — the per-file byte cap
# ---------------------------------------------------------------------------
# prune_logs only runs as a run starts, so nothing it does bounds the file
# being written: one idevicebackup2 or rsync error loop fills the rootfs within
# a single run. The writer caps its own file, says so in the file, and replays
# the last lines on close so the run's verdict still reaches the log.

def test_write_stops_at_the_per_file_cap(tmp_path):
    path = str(tmp_path / "sync-cap.log")
    cap = 64 * 1024
    with logutil.open_run_log(path, max_bytes=cap) as log:
        for i in range(5000):
            log.write(f"line {i} " + "x" * 80 + "\n")     # ~500 KB unbounded
    tail = min(logutil._CAPPED_TAIL_BYTES, cap // 8)
    # Read bytes with the newlines the device writes: the cap counts "\n", and
    # a Windows test host would otherwise land a byte per line over the bound.
    body = open(path, "rb").read().replace(b"\r\n", b"\n")
    assert len(body) <= cap + tail + 500           # cap + replayed tail + markers
    assert b"line 0 " in body.split(b"\n")[0]      # the start of the run is kept


def test_a_capped_log_says_it_was_truncated(tmp_path):
    """The marker has to be on disk the moment the cap is hit: update.sh
    stopping the services SIGKILLs the writer, which never reaches close()."""
    path = str(tmp_path / "sync-marker.log")
    log = logutil.open_run_log(path, max_bytes=2048)
    for i in range(500):
        log.write(f"noise {i}\n")
    with open(path) as f:                              # still open, not closed
        markers = [l for l in f.read().splitlines() if l.startswith("[logutil]")]
    assert len(markers) == 1 and "cap" in markers[0]
    log.close()


def test_a_capped_log_keeps_the_last_lines_of_the_run(tmp_path):
    path = str(tmp_path / "sync-tail.log")
    with logutil.open_run_log(path, max_bytes=1024) as log:
        for i in range(2000):
            log.write(f"chatter {i}\n")
        log.write("[OK] done\n")                       # the verdict, written last
    lines = open(path).read().splitlines()
    assert lines[-1].endswith("[OK] done")
    summary = [i for i, l in enumerate(lines) if "suppressed line(s)" in l]
    assert summary and summary[0] < len(lines) - 1     # summary, then the tail


def test_write_after_the_cap_never_raises():
    for fh in (_BoomFile(fail=False), _BoomFile()):     # good disk, then ENOSPC
        log = logutil.TimestampedLog(fh, max_bytes=32)
        for _ in range(50):
            log.write("some line of chatter\n")        # long past the cap
        log.close()                                     # replays the tail


def test_the_cap_counts_what_is_already_in_the_file(tmp_path):
    """Reopening a log (a same-second daemon restart, or a crash) must not hand
    the same file a fresh budget, or the cap never bites."""
    path = str(tmp_path / "backup-reopen.log")
    with open(path, "w") as f:
        f.write("x" * 4096)
    with logutil.open_run_log(path, max_bytes=4096) as log:
        log.write("one more line\n")
    assert open(path).read()[4096:].startswith("[logutil]")


def test_a_zero_cap_disables_it(tmp_path):
    path = str(tmp_path / "sync-uncapped.log")
    with logutil.open_run_log(path, max_bytes=0) as log:   # <= 0, as in prune_logs
        for i in range(200):
            log.write("x" * 100 + "\n")
    assert "[logutil]" not in open(path).read()
    assert os.path.getsize(path) > 20000


def test_an_unstamped_run_log_is_capped_too(tmp_path):
    """stamp=False is for a log that writes its own format; the cap still holds."""
    path = str(tmp_path / "backup-raw.log")
    with logutil.open_run_log(path, stamp=False, max_bytes=512) as log:
        for i in range(500):
            log.write(f"raw {i}\n")
    lines = open(path).read().splitlines()
    assert lines[0] == "raw 0"                         # verbatim, no stamp
    assert any(l.startswith("[logutil]") and "cap" in l for l in lines)


def test_the_per_file_cap_is_below_the_aggregate_cap():
    """What keeps prune_logs' size sweep off a log that is still being written."""
    assert 0 < logutil.LOG_MAX_BYTES_PER_FILE <= logutil.LOG_MAX_BYTES_PER_KIND


# --- the open run log is never pruned ------------------------------------------
# prune_logs' docstring promises the freshest file survives all three rules. The
# size sweep spared it; the age rule did not, so an appliance idle past
# max_age_days could delete the log the daemon still holds open.

def test_the_newest_log_survives_the_age_rule(tmp_path):
    old = tmp_path / "backup-20200101-000000.log"
    old.write_text("ancient" + chr(10))
    os.utime(old, (0, 0))                      # far older than any max_age
    logutil.prune_logs(str(tmp_path), keep_per_kind=50, max_age_days=90)
    assert old.exists(), "the only (and open) log was deleted by the age rule"


def test_older_logs_are_still_pruned_by_age(tmp_path):
    for name in ("backup-20200101-000000.log", "backup-20200102-000000.log"):
        p = tmp_path / name
        p.write_text("x" + chr(10))
        os.utime(p, (0, 0))
    newest = tmp_path / "backup-20990101-000000.log"
    newest.write_text("current" + chr(10))
    logutil.prune_logs(str(tmp_path), keep_per_kind=50, max_age_days=90)
    assert newest.exists()
    assert not (tmp_path / "backup-20200101-000000.log").exists()
    assert not (tmp_path / "backup-20200102-000000.log").exists()
