giovi321/ios-backup-machine/tests/test_daemon_hardening.py

"""Tests for the daemon-hardening pieces: loop watchdog, shutdown exit codes,
draw-failure fallback to headless, and the pre-backup gates.

iosbackupmachine.py is imported the same way test_display_wiring does it: real
module, with waveshare_epd / periphery stubbed only when they can't import on
this machine, against a throwaway config/runtime dir.
"""
import json
import os
import plistlib
import subprocess
import sys
import tempfile
import time
import types

import pytest

SANDBOX = tempfile.mkdtemp(prefix="ibm_hardening_")


def _load_daemon():
    os.makedirs(SANDBOX, exist_ok=True)
    cfg_path = os.path.join(SANDBOX, "config.yaml")
    with open(cfg_path, "w") as f:
        f.write("backup_dir: /tmp/b\nsync:\n  enabled: false\n")
    os.environ["IOSBACKUP_CONFIG"] = cfg_path
    os.environ["IOSBACKUP_RUNTIME_DIR"] = os.path.join(SANDBOX, "rt")
    os.environ["IOSBACKUP_LOG_DIR"] = os.path.join(SANDBOX, "log")
    os.makedirs(os.environ["IOSBACKUP_RUNTIME_DIR"], exist_ok=True)
    os.makedirs(os.environ["IOSBACKUP_LOG_DIR"], exist_ok=True)

    _stub_package("waveshare_epd", ["epd2in13_V4", "epdconfig"])
    _stub_package("periphery", ["gpio"],
                  attrs={"gpio": {"GPIOError": type("GPIOError", (Exception,), {})}})

    import iosbackupmachine
    return iosbackupmachine


def _stub_package(name, submodules, attrs=None):
    """Register a stand-in for `name` only if the real package cannot import."""
    try:
        __import__(name)
        return
    except Exception:
        pass
    pkg = types.ModuleType(name)
    for sub_name in submodules:
        sub = types.ModuleType(f"{name}.{sub_name}")
        for k, v in ((attrs or {}).get(sub_name) or {}).items():
            setattr(sub, k, v)
        sys.modules[f"{name}.{sub_name}"] = sub
        setattr(pkg, sub_name, sub)
    sys.modules[name] = pkg


try:
    ibm = _load_daemon()
except Exception as exc:  # pragma: no cover - environment without the runtime deps
    pytest.skip(f"display daemon not importable: {exc}", allow_module_level=True)


class FakePanel:
    def __init__(self):
        self.painted = []
        self.slept = False

    def draw(self, **kw):
        self.painted.append(kw.get("screen"))

    def draw_owner(self):
        self.painted.append("owner")

    def draw_updating(self):
        self.painted.append("updating")

    def sleep(self):
        self.slept = True


@pytest.fixture
def no_exit(monkeypatch):
    codes = []
    monkeypatch.setattr(ibm.os, "_exit", codes.append)
    return codes


# --- LoopWatchdog -------------------------------------------------------------

def test_watchdog_exits_1_when_the_loop_stalls():
    exits, logs = [], []
    t = [1000.0]
    wd = ibm.LoopWatchdog(stall_sec=10, exit_fn=exits.append,
                          time_fn=lambda: t[0], log_fn=logs.append)
    wd.beat()
    t[0] += 11
    assert wd.check() is True
    assert exits == [1]
    assert any("stalled" in m for m in logs)


def test_watchdog_stays_quiet_while_beats_arrive():
    exits = []
    t = [1000.0]
    wd = ibm.LoopWatchdog(stall_sec=10, exit_fn=exits.append,
                          time_fn=lambda: t[0], log_fn=lambda m: None)
    for _ in range(5):
        t[0] += 8
        wd.beat()
        assert wd.check() is False
    assert exits == []


def test_watchdog_check_is_exactly_at_threshold_not_before():
    exits = []
    t = [1000.0]
    wd = ibm.LoopWatchdog(stall_sec=10, exit_fn=exits.append,
                          time_fn=lambda: t[0], log_fn=lambda m: None)
    t[0] += 10          # exactly at the threshold: not yet stalled
    assert wd.check() is False
    t[0] += 0.1
    assert wd.check() is True
    assert exits == [1]


# --- shutdown exit-code plumbing ----------------------------------------------

def test_a_normal_shutdown_exits_zero(no_exit):
    panel = FakePanel()
    ibm.Animator(panel)._do_shutdown()
    assert no_exit == [0]
    assert panel.painted == ["owner"]
    assert panel.slept is True


def test_a_fatal_shutdown_exits_nonzero(no_exit):
    a = ibm.Animator(FakePanel())
    a.exit_code = 1
    a._do_shutdown()
    assert no_exit == [1]


def test_an_explicit_exit_code_wins_over_the_default(no_exit):
    ibm.Animator(FakePanel())._do_shutdown(exit_code=1)
    assert no_exit == [1]


def test_shutdown_terminates_a_running_backup_child(no_exit, monkeypatch):
    class FakeProc:
        def __init__(self):
            self.terminated = False

        def poll(self):
            return None

        def terminate(self):
            self.terminated = True

    proc = FakeProc()
    monkeypatch.setattr(ibm, "_backup_proc", proc)
    try:
        ibm.Animator(FakePanel())._do_shutdown()
    finally:
        monkeypatch.setattr(ibm, "_backup_proc", None)
    assert proc.terminated is True
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
